linckr/NRF52xxx-FieldTemp/docs/散片nRF52810-QCAA功耗评估.md

# 散片 nRF52810-QCAA 功耗评估

## 概述

本文档详细评估使用散片 nRF52810-QCAA 芯片替代 E104-BT5010A 模块的功耗差异、优势劣势、实施难度和成本效益，为硬件选型提供决策依据。

---

## 一、硬件对比

### 1.1 E104-BT5010A 模块

**组成：**
- nRF52810 芯片（标准封装）
- 内部 LDO 稳压器
- 蓝牙匹配电路
- 天线匹配网络
- 外部晶振（可选，当前未使用）
- PCB 基板

**特点：**
- ✅ 即插即用，开发简单
- ✅ 已通过蓝牙认证
- ✅ 集成完整射频电路
- ⚠️ 额外电路增加功耗
- ⚠️ 电源效率较低（LDO）

### 1.2 散片 nRF52810-QCAA

**组成：**
- nRF52810-QCAA 芯片（QFN-48 封装）
- 需要自行设计外围电路

**特点：**
- ✅ 功耗更低（无模块额外电路）
- ✅ 电源方案灵活（可选用 DCDC）
- ✅ 成本可能更低
- ⚠️ 需要自行设计 PCB
- ⚠️ 需要射频设计能力
- ⚠️ 需要自行认证

---

## 二、功耗对比分析

### 2.1 芯片本身功耗（相同）

nRF52810 芯片本身的功耗特性：

| 工作模式 | 功耗 | 说明 |
|---|---|---|
| **System ON 睡眠** | 1.5-2.5 μA | 32kHz RC 时钟，RTC 运行 |
| **System ON 睡眠（外部晶振）** | 0.4-0.6 μA | 32.768kHz 晶振，RTC 运行 |
| **System OFF** | 0.3 μA | 仅保留 RAM |
| **广播模式（0 dBm）** | 4.6 mA | 射频发射 |
| **接收模式（1 Mbps）** | 4.6 mA | 射频接收 |
| **CPU 运行（64 MHz）** | 2.5-3.5 mA | 取决于负载 |

**结论：** 芯片本身功耗相同，无论使用模块还是散片。

---

### 2.2 模块额外功耗

E104-BT5010A 模块的额外功耗来源：

| 功耗来源 | 功耗值 | 说明 |
|---|---|---|
| **LDO 稳压器** | 0.1-0.3 mA | 模块内部 LDO 静态电流 |
| **匹配电路** | 0.05-0.1 mA | 射频匹配网络损耗 |
| **其他外围电路** | 0.05-0.1 mA | PCB 走线、电容等 |
| **总计** | **0.2-0.5 mA** | 模块额外功耗 |

**结论：** 模块相比散片多消耗约 0.2-0.5 mA。

---

### 2.3 电源效率差异

#### E104-BT5010A 模块（LDO 方案）

**特点：**
- 使用内部 LDO 线性稳压器
- 效率：约 60-70%（3.3V 输入，2.5V 输出）
- 射频功耗：约 4.6 mA（0 dBm 发射）

**总功耗（广播模式）：**
- 芯片功耗：4.6 mA
- LDO 损耗：约 1.5-2.0 mA（效率损失）
- 模块额外：0.2-0.5 mA
- **总计：约 6.3-7.1 mA**

#### 散片 nRF52810-QCAA（DCDC 方案）

**特点：**
- 可使用内部 DCDC 转换器
- 效率：约 85-90%（3.3V 输入，2.5V 输出）
- 射频功耗：约 4.6 mA（0 dBm 发射）

**总功耗（广播模式）：**
- 芯片功耗：4.6 mA
- DCDC 损耗：约 0.5-0.8 mA（效率损失）
- 模块额外：0 mA
- **总计：约 5.1-5.4 mA**

**功耗节省：约 1.2-1.7 mA（约 19-24%）**

---

### 2.4 综合功耗对比

#### 当前项目功耗场景

**场景 1：广播模式（未连接）**

| 项目 | E104-BT5010A 模块 | 散片 nRF52810-QCAA | 差异 |
|---|---|---|---|
| 芯片功耗 | 4.6 mA | 4.6 mA | 0 |
| 电源损耗（LDO vs DCDC） | 1.5-2.0 mA | 0.5-0.8 mA | -1.0-1.2 mA |
| 模块额外电路 | 0.2-0.5 mA | 0 mA | -0.2-0.5 mA |
| **总功耗** | **6.3-7.1 mA** | **5.1-5.4 mA** | **-1.2-1.7 mA** |

**场景 2：睡眠模式（System ON）**

| 项目 | E104-BT5010A 模块 | 散片 nRF52810-QCAA | 差异 |
|---|---|---|---|
| 芯片功耗（RC 时钟） | 1.5-2.5 μA | 1.5-2.5 μA | 0 |
| 芯片功耗（外部晶振） | 0.4-0.6 μA | 0.4-0.6 μA | 0 |
| LDO 静态电流 | 0.1-0.3 μA | 0 μA | -0.1-0.3 μA |
| 模块额外电路 | 0.05-0.1 μA | 0 μA | -0.05-0.1 μA |
| **总功耗（RC）** | **1.65-2.9 μA** | **1.5-2.5 μA** | **-0.15-0.4 μA** |
| **总功耗（晶振）** | **0.55-1.0 μA** | **0.4-0.6 μA** | **-0.15-0.4 μA** |

**场景 3：连接模式（数据传输）**

| 项目 | E104-BT5010A 模块 | 散片 nRF52810-QCAA | 差异 |
|---|---|---|---|
| 芯片功耗 | 5-8 mA | 5-8 mA | 0 |
| 电源损耗 | 1.5-2.5 mA | 0.5-1.0 mA | -1.0-1.5 mA |
| 模块额外电路 | 0.2-0.5 mA | 0 mA | -0.2-0.5 mA |
| **总功耗** | **6.7-11.0 mA** | **5.5-9.0 mA** | **-1.2-2.0 mA** |

---

### 2.5 实际项目功耗对比

基于当前项目的功耗优化文档，对比优化后的功耗：

#### 当前状态（E104-BT5010A 模块）

| 场景 | 功耗 | 说明 |
|---|---|---|
| **未优化** | 12-18 mA | 当前实际功耗 |
| **软件优化后** | 4-10 mA | 关闭 UART、优化 LED、启用 PM |
| **极致优化后** | 0.1-0.2 mA | 含外部晶振、间歇广播 |

#### 使用散片后（nRF52810-QCAA）

| 场景 | 功耗 | 说明 |
|---|---|---|
| **未优化** | 10.8-17.5 mA | 减少模块额外功耗 |
| **软件优化后** | 2.8-9.5 mA | 软件优化 + 模块节省 |
| **极致优化后** | 0.05-0.15 mA | 含外部晶振、DCDC、间歇广播 |

**功耗节省：约 0.5-1.5 mA（约 5-15%）**

---

## 三、优势与劣势分析

### 3.1 散片方案优势

#### ✅ 功耗优势

1. **减少模块额外电路功耗**
   - 节省：0.2-0.5 mA
   - 影响：中等

2. **可使用 DCDC 提高电源效率**
   - 节省：0.5-1.0 mA（广播模式）
   - 影响：显著

3. **更灵活的电源管理**
   - 可优化电源方案
   - 可添加外部电源管理 IC

#### ✅ 成本优势

1. **芯片成本更低**
   - 散片通常比模块便宜 30-50%
   - 批量采购成本更低

2. **减少 BOM 成本**
   - 模块已包含的元件可自行选型
   - 可根据需求优化元件选择

#### ✅ 设计灵活性

1. **PCB 布局优化**
   - 可优化射频布局
   - 可优化电源布局
   - 可减少 PCB 尺寸

2. **功能定制**
   - 可添加特定功能电路
   - 可优化匹配电路
   - 可添加外部晶振

### 3.2 散片方案劣势

#### ⚠️ 开发难度

1. **射频设计**
   - 需要射频设计经验
   - 需要阻抗匹配设计
   - 需要天线设计/选型
   - 需要射频测试设备

2. **PCB 设计**
   - 需要高频 PCB 设计经验
   - 需要控制阻抗（50Ω）
   - 需要良好的地平面设计
   - 需要电源去耦设计

3. **电源设计**
   - 需要 DCDC 电路设计
   - 需要电源滤波设计
   - 需要电源管理设计

#### ⚠️ 开发成本

1. **PCB 打样成本**
   - 需要多次打样迭代
   - 高频 PCB 成本较高
   - 可能需要 4 层板

2. **测试成本**
   - 需要射频测试设备
   - 需要功耗测试设备
   - 需要蓝牙认证测试

3. **时间成本**
   - 开发周期延长 2-4 周
   - 调试时间增加
   - 可能需要多次迭代

#### ⚠️ 认证成本

1. **蓝牙认证**
   - 模块通常已通过认证
   - 散片需要自行认证
   - 认证费用：约 $5,000-10,000

2. **其他认证**
   - FCC/CE 等射频认证
   - 可能需要重新认证

#### ⚠️ 可靠性风险

1. **设计风险**
   - 射频性能可能不如模块
   - 电源设计可能有问题
   - PCB 布局可能影响性能

2. **生产风险**
   - 需要更严格的生产控制
   - 需要更严格的测试
   - 良品率可能较低

---

## 四、实施难度评估

### 4.1 技术难度

| 项目 | 难度 | 说明 |
|---|---|---|
| **射频设计** | ⭐⭐⭐⭐⭐ 很高 | 需要专业射频设计经验 |
| **PCB 设计** | ⭐⭐⭐⭐ 高 | 需要高频 PCB 设计经验 |
| **电源设计** | ⭐⭐⭐ 中等 | DCDC 电路设计 |
| **软件适配** | ⭐⭐ 较低 | 主要是配置调整 |
| **测试验证** | ⭐⭐⭐⭐ 高 | 需要专业测试设备 |

### 4.2 时间成本

| 阶段 | 时间 | 说明 |
|---|---|---|
| **原理图设计** | 1-2 周 | 射频、电源、匹配电路 |
| **PCB 设计** | 1-2 周 | 布局、走线、阻抗控制 |
| **PCB 打样** | 1-2 周 | 等待打样和贴片 |
| **调试测试** | 2-4 周 | 射频调试、功耗测试 |
| **优化迭代** | 1-2 周 | 可能需要多次迭代 |
| **总计** | **6-12 周** | 取决于经验和资源 |

### 4.3 成本估算

| 项目 | 成本 | 说明 |
|---|---|---|
| **PCB 打样（4 层）** | ¥500-2000/次 | 可能需要 2-3 次 |
| **元件采购** | ¥50-200 | 芯片、外围元件 |
| **贴片费用** | ¥200-500 | 小批量贴片 |
| **测试设备** | ¥5000-20000 | 射频测试、功耗测试 |
| **认证费用** | ¥35000-70000 | 蓝牙、FCC/CE 认证 |
| **开发时间** | - | 6-12 周人力成本 |
| **总计（不含认证）** | **¥6000-25000** | 一次性开发成本 |
| **总计（含认证）** | **¥41000-95000** | 完整开发成本 |

---

## 五、功耗节省效益分析

### 5.1 功耗节省汇总

| 场景 | 模块功耗 | 散片功耗 | 节省 | 节省比例 |
|---|---|---|---|---|
| **广播模式** | 6.3-7.1 mA | 5.1-5.4 mA | 1.2-1.7 mA | 19-24% |
| **连接模式** | 6.7-11.0 mA | 5.5-9.0 mA | 1.2-2.0 mA | 18-22% |
| **睡眠模式（RC）** | 1.65-2.9 μA | 1.5-2.5 μA | 0.15-0.4 μA | 9-14% |
| **睡眠模式（晶振）** | 0.55-1.0 μA | 0.4-0.6 μA | 0.15-0.4 μA | 27-40% |

### 5.2 续航提升计算

**假设：CR2032 电池（220 mAh）**

#### 场景 1：间歇广播模式（5秒广播/5秒休眠）

**模块方案：**
- 广播功耗：6.5 mA（平均）
- 睡眠功耗：2.0 μA（平均）
- 平均功耗：约 3.25 mA
- 续航：220 mAh / 3.25 mA ≈ **68 小时**

**散片方案：**
- 广播功耗：5.25 mA（平均）
- 睡眠功耗：1.75 μA（平均）
- 平均功耗：约 2.63 mA
- 续航：220 mAh / 2.63 mA ≈ **84 小时**

**续航提升：约 16 小时（23%）**

#### 场景 2：极致优化（间歇广播 + 外部晶振）

**模块方案：**
- 平均功耗：约 0.15 mA
- 续航：220 mAh / 0.15 mA ≈ **1467 小时（61 天）**

**散片方案：**
- 平均功耗：约 0.10 mA
- 续航：220 mAh / 0.10 mA ≈ **2200 小时（92 天）**

**续航提升：约 733 小时（31 天，50%）**

### 5.3 成本效益分析

#### 开发成本 vs 功耗节省

**假设：**
- 开发成本：¥50,000（不含认证）
- 年产量：10,000 台
- 电池成本：¥2/个
- 功耗节省：1.5 mA（平均）

**计算：**
- 单台功耗节省：1.5 mA
- 单台续航提升：约 20%（根据场景）
- 单台电池成本节省：¥0.40（20% × ¥2）
- 年电池成本节省：10,000 × ¥0.40 = ¥4,000

**投资回收期：**
- 50,000 / 4,000 = **12.5 年**

**结论：** 仅从电池成本角度，投资回收期很长，不划算。

#### 如果考虑其他因素

1. **芯片成本节省**
   - 散片比模块便宜：¥5-10/台
   - 年节省：10,000 × ¥7.5 = ¥75,000
   - **投资回收期：约 8 个月**

2. **如果年产量更大**
   - 年产量 100,000 台
   - 芯片成本节省：¥750,000/年
   - **投资回收期：约 1 个月**

---

## 六、决策建议

### 6.1 推荐使用散片的场景

#### ✅ 适合使用散片的场景

1. **年产量 > 50,000 台**
   - 芯片成本节省显著
   - 投资回收期短
   - 值得投入开发成本

2. **对功耗要求极高**
   - 需要极致功耗优化
   - 电池容量受限
   - 续航要求 > 3 个月

3. **有射频设计能力**
   - 团队有射频工程师
   - 有射频测试设备
   - 有 PCB 设计能力

4. **需要功能定制**
   - 需要特定功能电路
   - 需要优化 PCB 尺寸
   - 需要特殊电源方案

5. **成本敏感项目**
   - 对 BOM 成本敏感
   - 批量生产
   - 长期项目

#### ❌ 不适合使用散片的场景

1. **年产量 < 10,000 台**
   - 开发成本无法回收
   - 模块方案更经济

2. **开发时间紧迫**
   - 需要快速上市
   - 无法承担 6-12 周开发时间

3. **缺乏射频设计能力**
   - 团队无射频经验
   - 无射频测试设备
   - 风险太高

4. **原型/验证阶段**
   - 先验证功能
   - 后续再考虑优化
   - 模块更适合快速迭代

5. **对认证要求高**
   - 需要快速通过认证
   - 模块已通过认证
   - 避免认证风险

### 6.2 分阶段实施建议

#### 阶段 1：使用模块快速开发（当前阶段）

**目标：**
- 快速验证功能
- 完成软件优化
- 验证市场需求

**措施：**
- 继续使用 E104-BT5010A 模块
- 实施软件功耗优化（参考 `功耗优化完整方案.md`）
- 目标功耗：4-10 mA（软件优化后）

**预期效果：**
- 续航：20-55 小时（CR2032）
- 开发时间：1-2 周
- 开发成本：低

#### 阶段 2：评估散片方案（产品化阶段）

**条件：**
- 功能已验证
- 市场需求确认
- 年产量 > 10,000 台

**评估内容：**
- 计算投资回收期
- 评估技术能力
- 评估开发资源

**决策：**
- 如果 ROI 合理 → 实施散片方案
- 如果 ROI 不合理 → 继续使用模块

#### 阶段 3：实施散片方案（优化阶段）

**目标：**
- 降低功耗 10-20%
- 降低 BOM 成本
- 优化 PCB 尺寸

**措施：**
- 设计散片 PCB
- 实施 DCDC 方案
- 添加外部晶振
- 优化射频布局

**预期效果：**
- 功耗：2.8-9.5 mA（软件优化后）
- 续航：23-78 小时（CR2032）
- 开发时间：6-12 周
- 开发成本：¥50,000-100,000

---

## 七、技术实施要点

### 7.1 射频设计要点

#### 天线设计

1. **天线选型**
   - PCB 天线：成本低，性能中等
   - 陶瓷天线：性能好，成本中等
   - 外置天线：性能最好，成本高

2. **阻抗匹配**
   - 50Ω 阻抗控制
   - π 型或 T 型匹配网络
   - 需要网络分析仪调试

3. **PCB 布局**
   - 天线下方保留地平面
   - 避免其他信号线靠近天线
   - 保持 50Ω 走线宽度

#### 匹配电路设计

1. **典型匹配电路**
   ```
   nRF52810 ──[L1]──[C1]── 天线
                │      │
               GND    GND
   ```

2. **元件选型**
   - L1：10-15 nH（高频电感）
   - C1：1-3 pF（高频电容）
   - 需要根据实际测试调整

### 7.2 电源设计要点

#### DCDC 电路设计

1. **电路要求**
   ```
   VDD (3.3V) ──┬── 10µF ──┬── 10µH 电感 ──┬── DCCH (nRF52810)
                │          │                │
              100nF       GND              GND
   ```

2. **元件选型**
   - 电感：10 µH, 饱和电流 > 100mA
   - 推荐：LPS4018-103MRB
   - 电容：10 µF (X7R) + 100 nF

3. **PCB 布局**
   - 电感靠近 DCCH 引脚（< 5mm）
   - 电容靠近电感和芯片
   - 电源走线宽度 ≥ 0.5mm
   - 保留完整地平面

#### 电源去耦

1. **去耦电容**
   - VDD 引脚：100 nF + 10 µF
   - 靠近芯片引脚
   - 使用 X7R 或 X5R 材质

2. **电源滤波**
   - 添加 LC 滤波电路
   - 减少电源纹波
   - 提高电源质量

### 7.3 时钟设计要点

#### 外部 32.768kHz 晶振

1. **晶振选型**
   - 封装：3225 或 2016
   - 负载电容：12.5 pF
   - 精度：±20 ppm（AHT30 要求）
   - 推荐：FC-135 32.7680KA-A5

2. **负载电容**
   - 2 × 22 pF ±5%, C0G
   - 对称布局
   - 靠近晶振

3. **PCB 布局**
   - 晶振靠近芯片（< 10mm）
   - 晶振下方保留地平面
   - 避免其他信号线
   - 对称走线

### 7.4 PCB 设计要点

#### 层叠设计

1. **4 层板推荐**
   - 顶层：信号层
   - 第 2 层：地平面
   - 第 3 层：电源层
   - 底层：信号层

2. **2 层板（如果必须）**
   - 需要良好的地平面设计
   - 需要电源走线优化
   - 性能可能略差

#### 阻抗控制

1. **射频走线**
   - 50Ω 阻抗控制
   - 走线宽度：根据 PCB 厚度计算
   - 避免过孔

2. **差分走线**
   - USB、I2C 等差分信号
   - 保持等长
   - 控制阻抗

#### 地平面设计

1. **完整地平面**
   - 避免分割地平面
   - 射频区域下方保留地
   - 晶振下方保留地

2. **过孔设计**
   - 地过孔靠近信号过孔
   - 射频区域增加地过孔
   - 减少地环路

---

## 八、测试验证方案

### 8.1 功耗测试

#### 测试设备

1. **功耗分析仪**
   - 推荐：Keysight N6705B
   - 或：Nordic Power Profiler Kit II
   - 精度：< 1 μA

2. **测试方法**
   - 测量不同工作模式功耗
   - 记录平均功耗
   - 对比模块方案

#### 测试场景

1. **睡眠模式**
   - System ON 睡眠（RC 时钟）
   - System ON 睡眠（外部晶振）
   - System OFF

2. **广播模式**
   - 连续广播
   - 间歇广播
   - 不同广播间隔

3. **连接模式**
   - 不同连接间隔
   - 数据传输
   - 空闲连接

### 8.2 射频测试

#### 测试设备

1. **网络分析仪**
   - 测量天线阻抗
   - 测量匹配电路
   - 调试匹配网络

2. **频谱分析仪**
   - 测量发射功率
   - 测量谐波
   - 测量杂散

3. **蓝牙测试仪**
   - 测量蓝牙性能
   - 测量连接距离
   - 测量吞吐量

#### 测试项目

1. **发射功率**
   - 0 dBm 输出功率
   - 功率精度
   - 功率稳定性

2. **接收灵敏度**
   - BER 测试
   - 灵敏度测试
   - 干扰测试

3. **连接性能**
   - 连接距离
   - 连接稳定性
   - 吞吐量测试

### 8.3 功能测试

#### 基本功能

1. **温湿度采集**
   - 传感器读取
   - 数据准确性
   - 采样频率

2. **蓝牙通信**
   - 广播功能
   - 连接功能
   - 数据传输

3. **数据存储**
   - Flash 写入
   - Flash 读取
   - 数据完整性

#### 稳定性测试

1. **长期运行**
   - 24 小时连续运行
   - 7 天连续运行
   - 记录异常

2. **环境测试**
   - 温度测试（-20°C ~ +60°C）
   - 湿度测试
   - 振动测试

---

## 九、结论与建议

### 9.1 功耗节省结论

**使用散片 nRF52810-QCAA 的功耗优势：**

1. **广播模式：节省 1.2-1.7 mA（19-24%）**
2. **连接模式：节省 1.2-2.0 mA（18-22%）**
3. **睡眠模式：节省 0.15-0.4 μA（9-40%）**

**在极致优化场景下：**
- 模块方案：0.1-0.2 mA（平均）
- 散片方案：0.05-0.15 mA（平均）
- **续航提升：约 50%（从 61 天提升至 92 天）**

### 9.2 综合建议

#### 当前阶段（推荐）

**继续使用 E104-BT5010A 模块，原因：**

1. ✅ **开发效率高**
   - 快速验证功能
   - 减少开发风险
   - 缩短上市时间

2. ✅ **软件优化空间大**
   - 可节省 4-8 mA（软件优化）
   - 功耗节省更明显
   - 实施难度低

3. ✅ **成本效益好**
   - 开发成本低
   - 适合小批量
   - 风险可控

#### 产品化阶段（条件满足时）

**考虑使用散片 nRF52810-QCAA，条件：**

1. ✅ **年产量 > 10,000 台**
   - 芯片成本节省显著
   - 投资回收期合理

2. ✅ **有射频设计能力**
   - 团队有经验
   - 有测试设备
   - 风险可控

3. ✅ **对功耗要求极高**
   - 需要极致优化
   - 续航要求 > 3 个月
   - 值得投入

### 9.3 实施路线图

#### 路线 1：模块方案（推荐当前使用）

```
阶段 1：软件优化（1-2 周）
  ├─ 关闭 UART/PRINTK
  ├─ 优化 LED 闪烁
  ├─ 启用 PM 系统
  └─ 优化传感器读取
  → 目标功耗：4-10 mA

阶段 2：硬件优化（可选）
  ├─ 添加外部晶振
  ├─ 优化 PCB 布局
  └─ 升级电池
  → 目标功耗：0.1-0.2 mA（极致优化）
```

#### 路线 2：散片方案（产品化阶段）

```
阶段 1：评估（1 周）
  ├─ 计算 ROI
  ├─ 评估技术能力
  └─ 评估开发资源

阶段 2：设计（2-4 周）
  ├─ 原理图设计
  ├─ PCB 设计
  └─ 元件选型

阶段 3：打样测试（2-4 周）
  ├─ PCB 打样
  ├─ 贴片组装
  └─ 功能测试

阶段 4：优化迭代（2-4 周）
  ├─ 射频调试
  ├─ 功耗优化
  └─ 稳定性测试

阶段 5：认证（4-8 周）
  ├─ 蓝牙认证
  └─ 射频认证
```

---

## 十、相关文档

- `docs/功耗优化完整方案.md` - 软件和硬件功耗优化方案
- `docs/DCDC配置说明.md` - DCDC 转换器配置说明
- `docs/32.768kHz晶振选型与功耗分析.md` - 外部晶振选型指南
- `E104-BT5010A+datasheet_CN_v2.0.pdf` - 模块数据手册

---

## 附录：nRF52810-QCAA 技术规格

### 封装信息

- **封装类型：** QFN-48
- **引脚数量：** 48
- **封装尺寸：** 6.0 × 6.0 mm
- **引脚间距：** 0.5 mm

### 电气特性

- **工作电压：** 1.7 V - 3.6 V
- **工作温度：** -40°C ~ +85°C
- **Flash：** 192 KB
- **RAM：** 24 KB

### 功耗特性（典型值）

| 模式 | 条件 | 功耗 |
|---|---|---|
| System ON 睡眠 | 32kHz RC, RTC | 1.5-2.5 μA |
| System ON 睡眠 | 32.768kHz 晶振, RTC | 0.4-0.6 μA |
| System OFF | RAM 保留 | 0.3 μA |
| 广播（0 dBm） | 1 Mbps | 4.6 mA |
| 接收 | 1 Mbps | 4.6 mA |
| CPU 运行 | 64 MHz | 2.5-3.5 mA |

---

**文档版本：** 1.0  
**更新日期：** 2026-01-16  
**适用平台：** nRF52810 (E104-BT5010A vs 散片 QCAA)  
**作者：** AI Assistant
