linckr/NRF52xxx-FieldTemp/docs/温湿度传感器选型对比.md

# 温湿度传感器选型对比：AHT30 vs SHT40

## 快速对比表

| 特性 | AHT30 | SHT40 | 推荐场景 |
|---|---|---|---|
| **温度精度** | ±0.3°C | ±0.2°C | SHT40 更精确 |
| **湿度精度** | ±2%RH | ±1.8%RH | SHT40 更精确 |
| **测量时间** | 80ms | 1.7~8.2ms | SHT40 快 10 倍 |
| **功耗** | 较高 | 超低 (0.4μA 待机) | SHT40 更省电 |
| **价格** | 低 (约 ¥3-5) | 较高 (约 ¥8-12) | AHT30 性价比高 |
| **CRC 校验** | 无 | 有 | SHT40 更可靠 |
| **加热器** | 无 | 有 | SHT40 适合高湿环境 |
| **I2C 地址** | 0x38 (固定) | 0x44/0x45 (可选) | SHT40 更灵活 |
| **供电电压** | 2.0~5.5V | 1.08~3.6V | AHT30 范围更广 |
| **封装尺寸** | 3.0×3.0mm | 1.5×1.5mm | SHT40 更小 |

## 详细对比

### 1. 精度对比

#### 温度精度

| 传感器 | 典型精度 | 最大误差 | 测量范围 |
|---|---|---|---|
| AHT30 | ±0.3°C | ±0.5°C | -40~85°C |
| SHT40 | ±0.2°C | ±0.4°C | -40~125°C |

结论：SHT40 精度更高，测量范围更广。

#### 湿度精度

| 传感器 | 典型精度 | 最大误差 | 测量范围 |
|---|---|---|---|
| AHT30 | ±2%RH | ±3%RH | 0~100%RH |
| SHT40 | ±1.8%RH | ±3.5%RH | 0~100%RH |

结论：SHT40 典型精度更高，但最大误差略大。

### 2. 性能对比

#### 测量速度

```
AHT30: 80ms (固定)
SHT40: 1.7ms (低精度) / 4.5ms (中精度) / 8.2ms (高精度)
```

SHT40 即使在高精度模式下，也比 AHT30 快近 10 倍。

#### 功耗对比

| 模式 | AHT30 | SHT40 |
|---|---|---|
| 待机 | ~1μA | 0.4μA |
| 测量 (1次/秒) | ~1.5μA | 0.8μA (高精度) |
| 测量 (1次/秒) | ~1.5μA | 0.3μA (低精度) |

结论：SHT40 功耗更低，尤其适合电池供电应用。

### 3. 功能对比

#### AHT30 特点

- 简单易用，无需复杂配置
- 固定测量模式，无需选择精度
- 价格便宜，性价比高
- 供电电压范围广 (2.0~5.5V)
- 无 CRC 校验，可靠性稍低

#### SHT40 特点

- 三种精度模式可选，灵活性高
- 内置加热器，可去除冷凝
- CRC-8 校验，数据更可靠
- 测量速度快，响应迅速
- 功耗超低，适合低功耗应用
- 可选 I2C 地址，支持多传感器
- 价格较高

### 4. 应用场景推荐

#### 选择 AHT30 的场景

1. **成本敏感项目**
   - 大批量生产
   - 预算有限
   - 对精度要求不高

2. **简单应用**
   - 室内温湿度监测
   - 家用温湿度计
   - 教育项目

3. **宽电压供电**
   - 需要 5V 供电
   - 电源电压不稳定

4. **快速原型开发**
   - 简单易用
   - 无需复杂配置

#### 选择 SHT40 的场景

1. **高精度要求**
   - 实验室环境监测
   - 医疗设备
   - 精密仪器

2. **低功耗应用**
   - 电池供电设备
   - 无线传感器节点
   - 可穿戴设备

3. **快速响应**
   - 需要快速采样
   - 实时监控
   - 动态环境监测

4. **高湿度环境**
   - 需要加热器去除冷凝
   - 浴室、厨房等高湿场所
   - 户外应用

5. **高可靠性要求**
   - 需要 CRC 校验
   - 关键应用
   - 长期稳定运行

6. **多传感器系统**
   - 同一 I2C 总线上需要多个温湿度传感器
   - 利用可选地址功能

### 5. 代码对比

#### AHT30 使用示例

```c
// 初始化
aht30_init(i2c_dev);

// 读取数据 (固定 80ms)
int32_t temp, humi;
aht30_read(&temp, &humi);

printk("温度: %d.%02d °C\n", temp / 100, abs(temp % 100));
printk("湿度: %d.%02d %%RH\n", humi / 100, humi % 100);
```

#### SHT40 使用示例

```c
// 初始化 (需要指定地址)
sht40_init(i2c_dev, SHT40_I2C_ADDR_A);

// 读取数据 (可选精度)
int32_t temp, humi;
sht40_read(&temp, &humi, SHT40_PRECISION_HIGH);  // 8.2ms

printk("温度: %d.%02d °C\n", temp / 100, abs(temp % 100));
printk("湿度: %d.%02d %%RH\n", humi / 100, humi % 100);

// 高湿度环境使用加热器
if (humi > 9000) {
    sht40_read_with_heater(&temp, &humi, SHT40_HEATER_200MW_0_1S);
}
```

### 6. 成本分析

#### 单片成本 (参考价格)

| 传感器 | 小批量 (1-10片) | 中批量 (100片) | 大批量 (1000片+) |
|---|---|---|---|
| AHT30 | ¥5-8 | ¥3-5 | ¥2-3 |
| SHT40 | ¥12-15 | ¥8-10 | ¥6-8 |

#### 总体拥有成本 (TCO)

考虑以下因素：

1. **开发成本**
   - AHT30: 简单，开发快
   - SHT40: 功能多，需要更多测试

2. **功耗成本**
   - 电池供电应用中，SHT40 可延长电池寿命
   - 长期运行，SHT40 更省电

3. **可靠性成本**
   - SHT40 有 CRC 校验，减少错误数据
   - 减少售后维护成本

4. **性能收益**
   - SHT40 测量快，可提高系统响应速度
   - 高精度可提升产品竞争力

### 7. 迁移建议

#### 从 AHT30 迁移到 SHT40

如果你的项目已经使用 AHT30，但需要更高性能，迁移很简单：

```c
// 原 AHT30 代码
aht30_init(i2c_dev);
aht30_read(&temp, &humi);

// 迁移到 SHT40 (最小改动)
sht40_init(i2c_dev, SHT40_I2C_ADDR_A);
sht40_read(&temp, &humi, SHT40_PRECISION_HIGH);
```

主要改动：
1. 初始化时指定 I2C 地址
2. 读取时选择精度模式
3. 可选：利用加热器功能
4. 可选：读取序列号

#### 硬件改动

- I2C 地址不同 (AHT30: 0x38, SHT40: 0x44)
- 封装尺寸不同 (需要修改 PCB)
- 引脚兼容 (VDD, GND, SCL, SDA)

### 8. 推荐决策树

```
开始
  |
  ├─ 预算有限？
  |    └─ 是 → 选择 AHT30
  |
  ├─ 需要高精度？
  |    └─ 是 → 选择 SHT40
  |
  ├─ 电池供电？
  |    └─ 是 → 选择 SHT40
  |
  ├─ 需要快速响应？
  |    └─ 是 → 选择 SHT40
  |
  ├─ 高湿度环境？
  |    └─ 是 → 选择 SHT40 (有加热器)
  |
  ├─ 需要多个传感器？
  |    └─ 是 → 选择 SHT40 (可选地址)
  |
  └─ 简单应用？
       └─ 是 → 选择 AHT30
```

## 总结

### AHT30 适合：
- 成本敏感项目
- 简单温湿度监测
- 快速原型开发
- 对精度要求不高的场景

### SHT40 适合：
- 高精度要求
- 低功耗应用
- 快速响应需求
- 高湿度环境
- 高可靠性要求
- 多传感器系统

### 最终建议

1. **新项目**: 优先考虑 SHT40，性能更好，功耗更低
2. **成本敏感**: 选择 AHT30，性价比高
3. **高端产品**: 选择 SHT40，提升产品竞争力
4. **大批量生产**: 根据成本和性能需求权衡

两款传感器都是优秀的选择，关键是根据你的具体需求和预算做出决策。
