linckr/NRF52xxx-FieldTemp/PROTOCOL.md

# PROTOCOL.md — Firmware ↔ Android 接口协议

> 本文**从固件与 Android 两端代码逐字段交叉核对**得出，不是设计稿。
> 核对来源：
> - 固件：`src/ble/ble_ota.h`、`src/ble/ble_ota.c`、`src/ble/ble_services.h`、`src/main.c`、
>   `src/common.h`、`src/storage/w25q64.h`
> - Android：`data/bluetooth/BleConstants.kt`、`data/device/parser/*.kt`、`data/ota/*.kt`
>
> 全部数值一律 **小端序（little-endian）**，除非特别注明。

---

## 0. 总览：服务与特征

| 服务 | 服务 UUID | 特征 | 特征 UUID | 属性 | CCC | 用途 |
|---|---|---|---|---|---|---|
| 配置 | `12340020-1234-5678-1234-56789abcdef0` | 历史记录间隔 | `12340021-…` | READ / WRITE | 无 | uint16 秒（60~3600） |
| | | 设备状态 | `12340022-…` | READ / NOTIFY | 有 | 12 B |
| | | 历史数据 | `12340023-…` | WRITE / NOTIFY | 有 | 写 4 B timestamp / 5 B 显式请求；通知最多60 B |
| | | 温度极值 | `12340024-…` | READ / NOTIFY | 有 | 12 B |
| | | 温度极值重置 | `12340025-…` | WRITE | 无 | 写任意值即重置 |
| | | 历史信息 | `12340026-…` | READ | 无 | 8 B |
| | | **时间同步** | `12340011-…` | WRITE | 无 | 4 B Unix 秒 |
| 实时数据 | `12340030-1234-5678-1234-56789abcdef0` | 实时数据 | `12340031-…` | READ / NOTIFY | 有 | **8 B**（6 B 基础 + 2 B 电压） |
| 清空数据 | `12340040-1234-5678-1234-56789abcdef0` | 清空数据 | `12340041-…` | WRITE | 无 | 未启用保留时写任意非空值异步清空；保留启用后拒绝 |
| **OTA** | `12340050-1234-5678-1234-56789abcdef0` | Control | `12340051-…` | WRITE | 无 | 控制命令 |
| | | Data | `12340052-…` | **WRITE WITHOUT RESPONSE** | 无 | 镜像分片 |
| | | Status | `12340053-…` | NOTIFY | 有 | 12 B 状态 |

UUID 全称规则：`1234 00XX 1234 5678 1234 56789abcdef0`，完整写法例如
`12340021-1234-5678-1234-56789abcdef0`。固件与 Android 各自声明这些 UUID；任何变更都必须
同时核对 `ble_services.h` / `ble_ota.h` 与 `BleConstants.kt`。

### 时间同步与电池电压的归属

- 固件没有 `12340010` 服务；时间同步特征 `12340011` 属于配置服务 `12340020`。
- `12340026` 只表示历史信息。Android 已删除早期与它冲突的 `BATTERY_CHAR` 别名。
- 电池电压通过实时数据帧的 offset 6 上报。

---

## 1. 广播与设备名

| 项目 | 值 |
|---|---|
| 广播名 | `PandaTemp_XXXX`，`XXXX` = `%02X%02X` 形式的蓝牙地址低两字节（**反序**：`val[1]` 在前） |
| 名称来源 | `src/ble/ble_adv.c:60`，`snprintf(..., "%s_%02X%02X", DEVICE_NAME_BASE, addrs[0].a.val[1], addrs[0].a.val[0])` |
| 实测例 | `PandaTemp_7086` |
| 连接数 | `CONFIG_BT_MAX_CONN=1` —— **同一时刻只允许 1 个连接** |
| 配对/绑定 | 关闭（`CONFIG_BT_SMP=n`、`CONFIG_BT_BONDABLE=n`、`CONFIG_BT_MAX_PAIRED=0`），**无加密** |
| 广播标志 | `BT_LE_AD_GENERAL | BT_LE_AD_NO_BREDR` |

Android 侧的名称过滤常量（`BleConstants`）：`PandaTemperatureEX` / `PandaTemperature` /
前缀 `Panda` / `yodfz-temp` / 前缀 `yodfz`。当前固件名 `PandaTemp_7086` 命中前缀 `Panda`。

---

## 2. 配置服务

### 2.1 历史记录间隔 `12340021`（READ / WRITE，uint16）

| 偏移 | 长度 | 类型 | 端序 | 说明 |
|---|---:|---|---|---|
| 0 | 2 | uint16 | LE | 历史记录落盘周期（秒） |

- 有效范围 **60 ~ 3600**（`MIN_HISTORY_INTERVAL = 60`，`MAX_HISTORY_INTERVAL = 3600`）。
  下限 60 是**容量红线**（65000 × 60 s = 45.1 天，产品承诺 30 天），不是性能取舍。
- 写入后固件会**立即通知**同特征上的新值（`interval_char_data`）。
- ⚠️ 语义变更：旧固件（v2 及更早）该特征表示"采集间隔"，采样与落盘共用同一周期。
  新固件（1.0.6+0 起）表示"历史记录落盘周期"，采样**固定 1 秒**。
  App 通过状态帧 `byte5` 的 `bit0 (CAP_HISTORY_INTERVAL)` 区分。

### 2.2 设备状态 `12340022`（READ / NOTIFY，**12 字节**）

| 偏移 | 长度 | 类型 | 端序 | 说明 |
|---|---:|---|---|---|
| 0 | 2 | uint16 | LE | 历史记录间隔（秒） |
| 2 | 2 | uint16 | LE | 已存储记录数（超过 65535 时截断为 0xFFFF） |
| 4 | 1 | uint8 | — | 状态位，见下表 |
| 5 | 1 | uint8 | — | 能力位，见下表（旧固件恒 0） |
| 6 | 2 | uint16 | LE | 固件版本号 —— **新固件为 patch 号**（1.0.8 → `8`；旧固件为主/次编码） |
| 8 | 2 | uint16 | LE | 采样间隔（恒为 `1`） |
| 10 | 2 | uint16 | LE | 名义天数：启用策略按limit，否则按65000；capacity×interval/86400取整，上限0xFFFF |

**byte4 状态位**

| Bit | 宏 | 含义 |
|---|---|---|
| 0 | — | 已连接（`bt_connected`） |
| 1 | — | 时间已同步（含仅从 NVS 恢复的旧时间） |
| 2 | — | 正在清空或执行历史保留维护；忙时暂停历史请求 |
| 3 | — | **墙钟可信**：本次上电收到过手机对时。仅从 NVS 恢复旧时间时为 0 |

**byte5 能力位**（`src/main.c:882-887`）

| Bit | 宏 | 含义 |
|---|---|---|
| 0 | `CAP_HISTORY_INTERVAL 0x01` | `12340021` 已改为"历史记录间隔"语义 |
| 1 | `CAP_SAMPLE_FIXED 0x02` | 采样固定 1 秒，不可配置 |
| 2 | `CAP_EVENT_RECORDS 0x04` | 支持突变/越限事件记录 |
| 3 | `CAP_AVERAGE_RECORDS 0x08` | 历史记录为周期均值 |
| 4 | `CAP_WALLCLOCK_ALIGN 0x10` | 周期记录时间戳按墙钟边界对齐（60→`:00`；300→`:00/:05/…） |
| 5 | `CAP_PARTIAL_WINDOW 0x20` | 对时后首个窗口可能短于一个周期（保留而非丢弃） |
| 6 | `CAP_HISTORY_VOLTAGE 0x40` | 支持显式请求14 B含电压历史；不能仅凭此位假定已协商 |
| 7 | `CAP_HISTORY_RETENTION 0x80` | 支持HISTORY特征的持续3000条保留命令 |

源码 v9 上报 `caps = 0xFF`；v8 历史基线为 `0x3F`。新固件已真机运行，cap255与V3 raw3000条回读通过；保留冷启动持久性已通过真实断电及raw集合验证；数据库迁移已完成，最新Live回归通过。

Android 解析：`DeviceStatusParser`（支持 5 / 7 / 8 / 10 / 12 字节，缺失字段取默认值）。

### 2.3 历史信息 `12340026`（READ，**8 字节**）

| 偏移 | 长度 | 类型 | 端序 | 说明 |
|---|---:|---|---|---|
| 0 | 4 | uint32 | LE | 总记录数 |
| 4 | 2 | uint16 | LE | 起始扇区（有数据时为最旧扇区号，否则 0） |
| 6 | 2 | uint16 | LE | 起始记录索引（保留窗口可能为非0；从此精确位置开始读） |

### 2.4 温度极值 `12340024`（READ / NOTIFY，**12 字节**）

| 偏移 | 长度 | 类型 | 端序 | 说明 |
|---|---:|---|---|---|
| 0 | 2 | int16 | LE | 最高温度（0.01 °C） |
| 2 | 4 | uint32 | LE | 最高温度发生时间（Unix 秒） |
| 6 | 2 | int16 | LE | 最低温度（0.01 °C） |
| 8 | 4 | uint32 | LE | 最低温度发生时间（Unix 秒） |

特殊值（`MaxMinTempParser`）：最高温和 `-32768(0x8000)` 且时间戳 0 → 未记录/已重置；
最低温和 `32767(0x7FFF)` 且时间戳 0 → 未记录/已重置。

> 当前固件发送 12 字节。Android 解析器仍兼容旧固件的 4 字节格式。

### 2.5 温度极值重置 `12340025`（WRITE）

写入**任意长度任意内容**即触发重置，并通知手机新值。无固定报文格式。

### 2.6 时间同步 `12340011`（WRITE，**4 字节**）

| 偏移 | 长度 | 类型 | 端序 | 说明 |
|---|---:|---|---|---|
| 0 | 4 | uint32 | LE | Unix 时间戳（秒） |

- 长度必须 **恰好 4**，否则返回 `BT_ATT_ERR_INVALID_ATTRIBUTE_LEN`。
- 小于 `946684800`（2000-01-01 UTC）时**只打印警告、仍然接受**。
- 效果：置 `time_base_timestamp` / `time_base_uptime`、`time_synced = true`、
  **`wall_clock_aligned = true`**（状态帧 bit3 置 1）、**重算历史结算网格**、立即写入 NVS。
- 只动聚合窗口与结算网格，**不碰 NVS 写头与已有历史**。

### 2.7 清空数据 `12340041`（WRITE）

未启用保留策略且无维护任务时，写入任意非空值即触发**异步**清空（`clear_data_work_handler`，逐扇区擦除 256 个扇区）。
立即返回，不阻塞 GATT 响应。清空期间状态帧 bit2 置 1。
无固定报文格式。

---

## 3. 历史数据（`12340023`）

### 3.1 BLE 记录格式：V2 12 B / V3 14 B

| 偏移 | 长度 | 类型 | 说明 |
|---|---:|---|---|
| 0 | 4 | uint32 LE | Unix秒 |
| 4 | 2 | int16 LE | 温度0.01°C |
| 6 | 2 | uint16 LE | 湿度0.01%RH |
| 8 | 4 | uint32 LE | 气压Pa，发送时从存储字还原；App除100得到hPa |
| 12 | 2 | uint16 LE | 仅V3：采集时缓存电压mV；0xFFFF为未知/无效 |

旧存量没有历史电压，V3回读时填0xFFFF；不得用当前VDD补写旧记录。
App仅凭明确能力位及请求选格式，绝不按patch号或包长度猜测。

### 3.2 显式历史请求与通知

所有请求写 HISTORY `12340023`；offset必须为0，长度仅4或5 B。

| 请求 | 能力前提 | 含义 |
|---|---|---|
| `[timestamp LE32]` 4 B | 原有历史功能 | V2 12 B；0拉全量，正数只取timestamp更大的记录 |
| `[timestamp LE32, 03]` 5 B | `0x40` | 明确选择V3 14 B；timestamp语义同上 |
| `[3000 LE32, 04]` 5 B | `0x80`且操作已授权 | 启用持续保留最近3000条，不是历史timestamp请求 |

当前固件的保留命令只接受3000；60秒周期的3000条仅约2.08天，事件记录还可能缩短时间范围。旧固件拒绝5 B长度；发送新命令前必须核对能力，
**绝不能失败后回退写CLEAR `12340041`**：旧固件的CLEAR会对任意非空写入全量擦除。
未知尾操作码返回VALUE_NOT_ALLOWED；维护中、活动传输或无效保留数量返回WRITE_NOT_PERMITTED。
新连接默认V2；4 B请求恢复V2，5 B尾03只影响当前会话。格式请求须先成功，再启用CCC。

通知缓存仍60 B：V2最多5×12=60 B，V3最多4×14=56 B，尾包按整条记录截断。
结束标志仍为独立1 B `FF`，另有原有4 B总数通知，不属于历史记录。

### 3.3 Flash 内部编码：保持12 B，无批量迁移

`struct data_record`、地址跨度和页几何保持12 B、21条/页、336条/扇区。
只有offset8的32-bit存储字有新编码，**磁盘内容不再直接等同BLE气压字段**：

| bits31:30 | 含义 |
|---|---|
| `00` | 旧格式：完整uint32气压Pa；历史电压未知 |
| `11` | 新记录暂存，未提交，不可回传 |
| `10` | 新记录已提交；bits17:0气压Pa，bits29:18电压mV，4095为未知 |
| `01` | 不支持的格式，跳过 |

气压合法范围10000–200000 Pa，可用18 bits无损表示；电压12 bits可表示0–4094 mV。
先写暂存12 B并读回比对，再对offset11清bit6形成已提交标记，最后读回确认才推进有效写入。
整个12 B全FF才为空槽；非空撕裂槽占用、跳过，不在原地址覆盖。
提交已成功但应答失败时，重试识别相同已提交记录，不重复追加。
BLE发送先解码气压；旧App继续读12 B，不需要了解内部编码。
旧固件降级会将新编码气压判断为异常，不能作为支持的历史降级路径。

### 3.4 持续保留3000条：原子窗口与安全回收

原始记录必须先完整留档；裁剪不是自动连接操作，也不是全量清空。
收到合法命令后置状态byte4 bit2维护忙，分步从写头反向选择最近3000条有效已提交记录，
不足3000则保留全部。最近按存储顺序计算，不根据错误/未来年份猜排序。
独立NVS key7保存magic/version、limit、写头、精确首记录、数量和回收起点；旧keys1–3保持兼容。
提交并读回验证成功后，才回收窗口外完整旧扇区；首扇区旧前缀仅1→0零化，绝不擦除其有效尾部。
中途掉电重启时根据原子检查点及实际已占用/有效槽恢复窗口，回收幂等继续。
每次新记录提交后窗口前移；跨扇区才写检查点，不逐条改NVS。
历史信息总数、起始sector/index及新旧格式回读都遵守该窗口。
策略启用后CLEAR请求被拒绝，避免全量清空使持久化窗口失配。

此设计保持secondary/NVS/history既有地址及容量；native C故障注入通过不等同真实拔电验证，
已完成开发信任链 1.0.9 升级与主槽逐字节回读、V3 历史回读和硬件精确保留3000条；P3已取得擦除流程、部分写入、END后和暂停搬运流程的真实电池断电恢复证据，但不证明 NOR/NVMC 忙脉冲中断电。保留策略冷启动持久性已验证；realme到小米数据库迁移已完成；持续App3000策略retain验收通过，最新Live回归已通过；生产信任链部署待完成。 具体证据与测试边界见HANDOFF最新阶段记录。

---

## 4. 实时数据 `12340031`（READ / NOTIFY）

| 偏移 | 长度 | 类型 | 端序 | 说明 |
|---|---:|---|---|---|
| 0 | 2 | int16 | LE | 温度（0.01 °C，有符号） |
| 2 | 2 | uint16 | LE | 湿度（0.01 %RH） |
| 4 | 2 | uint16 | LE | 气压（**0.1 hPa**，由 Pa/10 得到，下限 0、上限 0xFFFF） |
| 6 | 2 | uint16 | LE | **电池电压（mV）** —— 仅当 `CONFIG_ADC=y` 时存在 |

- 帧长：`REALTIME_FRAME_LEN` = **8**（有 ADC）/ **6**（无 ADC）。当前发布构建为 **8**。
- 传感器读取失败时对应字段填 **0**（不是哨兵值）。
- 电压无效哨兵 **`0xFFFF`**；App 必须显示 `--`，绝不能显示成 65.535 V。
- ⚠️ 注意偏移 4 的单位与 §3.1 不同：**实时帧是 0.1 hPa，历史记录是 Pa**。
  这是历史遗留的不一致，两侧代码都按此解析，**当前不改**（改就是破坏兼容性）。
- 主动上报：需要在 `12340031` 上订阅 NOTIFY；1 Hz 采样触发通知。
  也可在 `12340031` 上直接 READ（读时现场刷新）。

Android 解析：`RealtimeDataParserV2`（`data/device/parser/RealtimeDataParser.kt`）。
它先判 `0xFFFF` 哨兵，再用 **1700~3600 mV** 量程做第二道防线（nRF52810 工作电压范围），
任一命中即置 `null`。

---

## 5. OTA 协议

服务 `12340050`，三特性：Control `12340051`（WRITE）、Data `12340052`（WRITE WITHOUT RESPONSE）、
Status `12340053`（NOTIFY）。

### 5.1 Control 命令（写 `12340051`）

| 操作码 | 名称 | 长度 | 有效状态 |
|---|---|---:|---|
| `0x01` | START | **61** | 任意（会中止上一次会话） |
| `0x02` | END | 1 | `READY` / `RECEIVING` |
| `0x03` | CANCEL | 1 | 任意 |
| `0x04` | TRIGGER | 1 | **仅 `VERIFY`** |

**START 报文（61 字节）**

| 偏移 | 长度 | 类型 | 端序 | 说明 |
|---|---:|---|---|---|
| 0 | 1 | uint8 | — | `0x01` |
| 1 | **16** | bytes | — | OTA 授权密钥（与固件 `OTA_AUTH_KEY` 逐字节相同） |
| 17 | 4 | uint32 | LE | 镜像总字节数 `total` |
| 21 | **8** | bytes | — | 镜像头偏移 `0x14` 起的 8 字节 `ih_ver`（**原样透传，不解析**） |
| 29 | **32** | bytes | — | **整个 `zephyr.signed.bin`** 的 SHA-256 |

长度不等于 61 → `err=9 (LEN)`；密钥不符 → `err=1 (AUTH)`。

**START 是异步的**：回调只做校验 + 拷贝 + `k_work_submit()`，整槽擦除（约 1~2 s）在工作队列执行。
**在收到 `state=READY` 之前，Data 写入会被拒绝**（回调返回 `BT_ATT_ERR_UNLIKELY`）。
客户端**必须**等 `READY`，`IDLE 且 err=0` 不等于可以发数据。

### 5.2 Data（写 `12340052`）

- 内容：`zephyr.signed.bin` 的顺序分片，纯追加，**无序号、无 offset、无每包校验**。
- 分片大小 = 协商 MTU − 3（ATT 写头）。MTU 128 → 125 B；回退 MTU 65 → 62 B。
- 只允许在 `READY` / `RECEIVING` 状态写。
- 累计字节数超过 START 声明的 `total` → `err=5 (SIZE)`。
- 环形缓冲（2 × 256 B）被打满 → **`err=11 (OVERRUN)` 保护性中止**（不静默丢数据），
  客户端应从 START 重发（设备按已确认偏移续传）。

### 5.3 Status 通知（`12340053`，**12 字节**）

| 偏移 | 长度 | 类型 | 端序 | 说明 |
|---|---:|---|---|---|
| 0 | 4 | uint32 | LE | **已写入 Flash 的连续偏移**（confirmed offset） |
| 4 | 4 | uint32 | LE | 镜像总字节数 `total` |
| 8 | 1 | uint8 | — | `state` |
| 9 | 1 | uint8 | — | `err` |
| 10 | 1 | uint8 | — | 进度百分比（`confirmed × 100 / total`） |
| 11 | 1 | uint8 | — | flags，**预留，恒 0** |

⚠️ `offset` 是**已落 Flash** 的连续偏移，**刻意滞后**于已接收字节数
（数据先进 256 B 缓冲，凑满一页才落盘）。**流控必须以它为准**，不能用"我发了多少"。

**发送时机**：`START` 完成（READY）、状态每次变化、以及**每收满 8 个 Data 包**
（`OTA_ACK_PACKETS = 8`）各通知一次。不逐包确认是刻意的（逐包 notify 会抢 ACL 缓冲与射频时间）。

**state（`enum ota_state`）**

| 值 | 名称 | 含义 |
|---:|---|---|
| 0 | `IDLE` | 空闲（START 准备期也报这个） |
| 1 | `READY` | 已擦除/已定位，**可以发数据** |
| 2 | `RECEIVING` | 接收中 |
| 3 | `VERIFY` | 字节数 / magic / 版本 / SHA-256 全部通过，可 TRIGGER |
| 4 | `PENDING` | 已 `boot_request_upgrade()`，即将重启 |
| 5 | `ERROR` | 出错，看 `err` |

**err（`enum ota_err`）**

| 值 | 名称 | 含义 |
|---:|---|---|
| 0 | `NONE` | 无错误 |
| 1 | `AUTH` | 密钥不匹配 |
| 2 | `STATE` | 当前状态不允许该操作 |
| 3 | `TOO_LARGE` | 超过次级槽容量（**擦除前**拒绝） |
| 4 | `FLASH` | 擦/写失败 |
| 5 | `SIZE` | 接收字节数与声明不符 |
| 6 | `MAGIC` | 镜像 magic 不对 |
| 7 | `VERSION` | 镜像 `ih_ver` 与 START 声明不符 |
| 8 | `HASH` | App 侧 SHA-256 校验失败（`CONFIG_IMG_ENABLE_IMAGE_CHECK=y` 时启用） |
| 9 | `LEN` | Control 报文长度非法 |
| 10 | `INTERNAL` | 内部错误 |
| 11 | `OVERRUN` | 接收环形缓冲被打满，保护性中止（可从已确认偏移重发 START 续传） |

### 5.4 断点续传

- 续传状态存在 **NVS `NVS_ID_OTA`**：

| 字段 | 类型 | 说明 |
|---|---|---|
| `offset` | uint32 | 已写入的连续偏移 |
| `total` | uint32 | 声明的总字节数 |
| `ih_ver[8]` | bytes | 镜像版本 |
| `img_id[16]` | bytes | **SHA-256 的前 16 字节** |
| `valid` | uint8 | 1 = 有效 |

- **续传判定必须同时比对 `total` + `ih_ver` + `img_id`**。
  只用 `(total, ih_ver)` 会把两个"同版本同大小但内容不同"的镜像错误拼接。
- 命中续传时，`resume_off = offset & ~(IMG_BLOCK_BUF_SIZE - 1)`（**向下对齐到 256 B**），
  **跳过整槽擦除**，从该偏移继续。
- 任一项不符 → 清掉续传状态、整槽重来。
- `CANCEL` 与 `TRIGGER` 都会清除续传状态。

### 5.5 重连 / 超时 / 重启

| 行为 | 固件侧 | Android 侧（`OtaRunner` / `OtaConstants`） |
|---|---|---|
| 断线重连 | 设备侧续传状态保留在 NVS，重连后重新 START 即可 | 每次重试**重新扫描**，不沿用旧 `BLEDevice` |
| 等待 READY 超时 | — | `START_READY_TIMEOUT_MS = 15_000` |
| Status 超时 | — | `statusTimeoutMs = 8_000`（构造参数默认值） |
| 流控窗口 | 每 8 包通知一次已落盘偏移 | `FLOW_WINDOW_BYTES = 4 KiB`（未确认字节不超过该值） |
| OVERRUN 重试 | 置 `err=11` 并停止接收 | `MAX_OVERRUN_RESTARTS = 2`（从已确认偏移续传重发） |
| MTU | 请求 128，失败回退默认 | `PREFERRED_MTU=128`、`FALLBACK_MTU=65`、`MIN_START_MTU=64` |
| TRIGGER 后 | `sys_reboot(SYS_REBOOT_WARM)` | 写 TRIGGER 后设备复位会拉断链路，**应判为成功**。表象有两种：BLE 写返回 `status=133 (GATT_ERROR)`（Android 侧，见 `TRIGGER_DISCONNECT_GRACE_MS=100` × 15 步），或 WinRT 直接抛 `OSError [WinError -2147467260]`（PC 侧，已由 `tools/ota_host_client.py` 捕获） |

### 5.6 镜像类型（**必须传 `zephyr.signed.bin`**）

Android **必须**发送 `zephyr.signed.bin`，不能是：

| 文件 | 为什么不行 |
|---|---|
| `zephyr.bin` | 裸应用镜像，**没有 MCUboot 头与签名** → 设备 `err=6 MAGIC` |
| `merged.hex` | 是 hex 文本且包含 MCUboot，格式与分区语义都不同 |
| `zephyr.elf` | 调试用 ELF |
| `dfu_application.zip` | 是给 MCUboot **serial recovery** 用的容器；当前未启用该模式 |

原因：设备把收到的字节**原样写进次级槽**，然后由 MCUboot 按固定头
（magic `0x96F3B83D`、`ih_hdr_size=512`、`ih_img_size`@`0x0C`、`ih_ver`@`0x14`）
解析并做 **ECDSA-P256 验签**。只有 `zephyr.signed.bin` 同时具备头与签名。

Android 侧 `OtaImageParser` 在**发送前**就校验 magic 与大小，magic 不符会直接以
`OtaImageError.BadMagic` 拒绝，而不是等设备报错。

---

## 6. 版本与兼容性协商

### 6.1 有没有独立的 protocol version？

**没有独立的 protocol version 字段，也没有单独的协商握手特征。** App 读取状态能力位后，在 HISTORY 请求中明确选择格式：`0x40` 能力位与 5 B 请求尾字节 `03` 共同启用 V3；只有能力位或版本号都不能代替该请求。`0x80` 则允许显式保留命令。
双方使用以下状态字段与服务信息判断能力：

| 判断依据 | 位置 | 说明 |
|---|---|---|
| 状态帧长度 | `12340022` 的读出长度 | 5 / 7 / 8 / 10 / 12 字节，缺字段取默认值 |
| 状态帧 `byte5` 能力位 | 见 §2.2 | 旧固件恒 0 → App 走旧语义分支 |
| 状态帧 `byte6–7` 固件版本 | uint16 LE，patch 号 | 显示与日志；有效版本号可参与 V1/V2 合并实时固件识别，不能推断 V3 |
| 实时帧长度 | `12340031` | ≥ 8 字节才读取电压字段 |
| 是否有实时数据服务 `12340030` | 服务发现 | 无则按老 ESS 固件处理 |
| OTA 服务 `12340050` 是否存在 | 服务发现 | 无则无 OTA 能力 |

⚠️ **固件版本号不能用来推断协议**：新固件是 **patch 号**（`APP_PATCHLEVEL`），
老固件是主/次版本编码，两者共用同一个 `uint16` 位段。这是本项目最容易踩的坑
（历史记录 V3 错位事故的根因）。

### 6.2 Android 如何判断固件版本

1. 读 `12340022` → `DeviceStatusParser` 读取 `byte6–7` 的 uint16 LE → `firmwareVersion`（新固件为 patch 号）。
2. 用于**界面显示**（`v9` 之类）与**日志**；`DeviceProfileFactory` 也将有效版本号（>0）或实时数据服务存在作为合并实时固件的 V2/V1 识别依据。
3. **不通过版本号推断 V3 或历史记录长度**：`0x40` 能力位明确选择 V3 Profile，其请求追加 `03`；没有该位时沿用 V2/V1 路径。

### 6.3 Android 如何判断 OTA 能力

服务发现时看是否存在 `12340050`。当前没有"OTA 能力位"这种东西。
`FirmwareUpdateScreen` 在有 OTA 服务时可用。

### 6.4 镜像兼容性 / 最低固件要求

- 镜像与设备的兼容性**完全由 MCUboot 保证**：分区大小（≤ 160 KiB 次级槽）+ `ih_ver` +
  ECDSA-P256 签名（必须由同一把私钥签出）。
- **没有**"最低固件版本"检查，也**没有**防回滚（downgrade prevention）配置。
  推一个版本号更低的已签名镜像，MCUboot 会正常搬运。
- 次级槽容量上限 `0x28000` = 163,840 B；App 签名镜像红线 157,696 B。

---

## 7. 错误与边界行为速查

| 场景 | 固件行为 | App 应如何处理 |
|---|---|---|
| 写入长度非法的 Control 报文 | `err=9`；START 长度不对时不改状态 | 按 `err` 文案提示 |
| Data 在非 READY/RECEIVING 时写入 | 回调返回 `BT_ATT_ERR_UNLIKELY`，**不发通知** | 超时 → 提示"设备未就绪" |
| 设备状态长时间停在 `IDLE` | START 正在擦除（1~2 s） | 等 READY，最多 15 s |
| 收到 `err=11 OVERRUN` | 已停止接收，Flash 中数据完整 | 提示后从 START 重发（自动续传），最多 2 次 |
| 收到 `err=8 HASH` | 次要校验失败（MCUboot 才是最终防线） | 提示重传，**设备不会重启** |
| TRIGGER 后链路断开（`status=133` / WinRT `已中止操作`） | 设备正常复位 | **判为成功**，不要报错 |
| 广播里看不到设备 | `MAX_CONN=1`，可能已被别的手机占用 | 先断开其它连接 |

---

## 8. 已清理的遗留冲突

2026-09-15 已同步修正 README 的 LED 引脚、最高最低温度特征长度、MCU 型号、历史气压字段名，
并删除冲突的 Android `BATTERY_CHAR` 与未注册的固件 `12340010` 声明。历史设计文档仍可能描述
旧协议；当前协议只以本文件与两端代码为准。`OTA_AUTH_KEY` 继续由忽略文件注入，固件可信边界
仍是 MCUboot ECDSA-P256 验签。

### 2026-10-10 当前验收状态：App 1.1.2 / 持续3000条

当前App为versionCode4 / versionName1.1.2、Room11，手机安装Debug APK；Firmware为开发信任链1.0.9。124项JVM单元测试、10项isolated Room测试通过；生产1.1.2 APK v2/RSA3072验签通过、证书未变，尚未安装生产APK。最新Live连续全量/立即重试/中途断连/重连回归171.105 s通过；最终归档结果见本节末。

手机已完成realme完整数据库到小米迁移（主库SHA匹配源归档），原小米1,042条GPS已备份、未并入。随后按完整归档及硬件raw集合应用精简；早先一次精简后App增至3004而硬件仍3000，确认一次性精简不足，现已实现持续策略。最新明确retain真机36.388 s通过：硬件3000、App模块3000、手机来源样本208；启用标记已持久化。手机样本包含有/无GPS，模块3000不等于整个数据库总行数；隔离记录及私人完整档案仍保留本机，不上传。

持续策略按device显式启用：仅在retain3000命令得到count=3000且idle确认后保存本地prefs。对已启用且支持0x80的设备，每次历史同步发timestamp=0全量请求；只有本会话真实END、received=3000、唯一wire timestamps=3000、前后原始8 B HISTORY_INFO完全一致、所有upsert成功及连接/会话仍属于捕获目标时，才事务删除不在该实际wire集合的模块行。删除ID每批最多500，失败/取消/切换设备全部回滚、不删除；窗口不稳定最多自动重试一次。不能按时间排序取3000，缓存行可能比设备窗口更新。启用标记仅代表策略启用，不能代替每次精简成功证据。

Room11的isPhoneSample采用INTEGER NOT NULL DEFAULT0；新手机实时行始终true，即使没有GPS。10→11无损迁移把已有GPS行标为phone，旧无GPS来源未知保守默认false；在完整归档后按真实wire集合核对，不能靠年份猜测删除。历史DAO/count/增量仅处理false且geoNull；所有phone/GPS、隔离表和其他设备受保护。严格核心数值断言曾阻止单行旧手机实时/硬件差异的错误精简，没有通过放宽断言绕过。测试覆盖来源保护、精确164缓存差集、1201条跨删除批次、SQL中段abort和session失效原子回滚。

硬件3000策略已在隔离整根SWD后的实际电池断电冷启动验证：archive_sync23.296 s、完整3000及核心/GPS/无重复/未来检查通过；再次raw19.434 s通过（3000 V3、42000 B、END、8 B INFO稳定）。此前小米1.1.0 archive_sync79.289 s通过是历史证据；当前1.1.2也已独立完成Live回归，见本节末。VDD2.765 V为10/9约18:45观测、2.875 V为10/10约00:17 VM观测，均非当前实时读数，ADC仍未校准/无万用表对照。

P3四阶段已取得擦除流程、部分写入、END后及暂停MCUboot搬运的真实电池断电恢复证据；不证明NOR WIP/NVMC写脉冲被切断。SWD仍连接时曾出现W25Q64 init_res=22，根因未定，隔离SWD重试通过不等于已定位。旧v8硬件尾部14条曾被覆盖，timestamp/传感器数值14/14均在本机完整App档案保全；新恢复函数已有真实C回归与冷启动证据。

固件资源保持App Flash151540 B、RAM23080 B（余1496 B），MCUboot31876 B（余892 B），分区不变。DEV signed候选152203 B已真机回读；生产asset152202 B未部署，DER长度可变。两镜像App payload151540 B逐字节一致，SHA256 `236323e4319f7228ce6b4856bb1736a4bede1cf58e3dfc85239678bdc943494c`；完整signed文件不能混同。生产imgtool验证通过，但生产MCUboot公钥信任尚未部署、候选产物入口为 [v1.0.9-rc.1](https://github.com/linckr/NRF52xxx-FieldTemp/releases/tag/v1.0.9-rc.1)，发布状态以页面为准；两个upstream PR #2在最近记录时OPEN，后续实时核对。

持续策略与Live验收已完成，最终归档模块3000；生产信任部署与ADC校准仍是独立待办。

### 最终Live与一致归档验收

最终真机Live回归171.105 s通过：两次连续全量各3000、立即重试、收到部分记录后断连且全部既有模块ID未删除、重连及再次同步完成3000；仍保留窗口内记录ID/核心字段和所有既有手机样本，无重复/未来时间。重连首轮观察到0条历史、随后一次自动全量重试成功；本轮已由有界重试覆盖，但首次重连延迟为Medium性能边界，根因未定位。

最终只读一致归档（2026-10-10约01:12）SQLite integrity ok：模块3000、GPS187、无GPS手机样本31（受保护手机样本共218）、active3218、quarantine22484，未来时间0、模块重复0。Live期间VM电压开始2.886 V、结束2.868 V（本轮观测，不是ADC校准证明）。App已恢复运行；手机临时USB亮屏设置已恢复原值。私人数据库、档案路径、标识与归档内容不进Git。
