linckr/NRF52xxx-FieldTemp/docs/2026-02-10-Flash存储校验修复计划-plan.md

# Flash存储校验修复计划

## 需求背景

用户反馈设备显示存储了 12 条记录，但无法获取数据（读取失败或无数据返回）。
经分析，原因是启动时 `storage_init` 函数中的 NVS 位置校验逻辑存在缺陷：仅校验了写头位置是否为 `0xFF`（空），未校验写头之前的记录是否有效。
如果 Flash 被意外擦除（全 `0xFF`），但 NVS 中仍保留了之前的写入位置（如 `next_record_in_sector = 12`），校验会错误地通过，导致系统认为有数据，但在读取时遇到 `0xFF` 而失败。

## 实现方案

修改 `src/main.c` 中的 `storage_init` 函数，增强 NVS 位置校验逻辑：

1. 在校验写头位置为 `0xFF` 的同时，如果 `next_record_in_sector > 0`，额外校验前一条记录（`next_record_in_sector - 1`）是否有效（非 `0xFF`）。
2. 如果前一条记录也是 `0xFF`，说明 NVS 记录的位置无效（数据已丢失），应视为校验失败。
3. 校验失败后，系统会自动进入“重新定位”逻辑（二分法查找实际数据末尾），从而正确重置存储位置（归零或找到真实数据末尾）。

## 开发计划

- [x] 修改 `src/main.c` 中的 `storage_init` 函数，添加前一条记录的校验逻辑。
- [x] 验证编译通过。
