linckr/NRF52xxx-FieldTemp/docs/手机端温度计实现方案对比.md

# 手机端温度计实现方案对比（2026 年）

## 1. 需求分析

### 1.1 核心需求

- ✅ 支持 iOS 和 Android 双平台
- ✅ 无网环境下正常运行
- ✅ 通过蓝牙连接 E104-BT5010A 温湿度采集设备
- ✅ 实时显示温湿度数据
- ✅ 历史数据查看和管理

### 1.2 技术约束

- 设备：E104-BT5010A (nRF52810, BLE 5.0)
- 通讯协议：BLE GATT
- 运行环境：可能无网络连接
- 目标平台：iOS 13+ / Android 8.0+

---

## 2. 技术方案对比

### 方案一：原生 App 开发

#### 2.1 iOS 原生开发 (Swift/SwiftUI)

**技术栈：**

- Swift 5.9+ / SwiftUI
- Core Bluetooth 框架
- Xcode 15+

**优势：**

- ✅ **性能最优**：直接调用系统 API，无中间层损耗
- ✅ **功能完整**：完整访问 iOS 蓝牙 API，支持所有 BLE 特性
- ✅ **用户体验好**：原生 UI，流畅度高
- ✅ **离线运行**：完全本地运行，无需网络
- ✅ **系统集成**：可集成 iOS 通知、后台运行等特性
- ✅ **安全性高**：App Store 审核严格，用户信任度高
- ✅ **长期维护**：Apple 长期支持，API 稳定

**劣势：**

- ❌ **开发成本高**：需要分别开发 iOS 和 Android 版本
- ❌ **开发周期长**：两个平台需要两套代码
- ❌ **维护成本高**：需要维护两套代码库
- ❌ **技能要求高**：需要掌握 Swift 和 Java/Kotlin
- ❌ **发布流程复杂**：需要分别提交 App Store 和 Google Play

**适用场景：**

- 对性能要求极高
- 需要深度系统集成
- 有充足的开发资源
- 长期维护的产品

**开发示例：**

```swift
import CoreBluetooth

class BLEManager: NSObject, CBCentralManagerDelegate, CBPeripheralDelegate {
    var centralManager: CBCentralManager!
    var peripheral: CBPeripheral?

    func startScan() {
        centralManager.scanForPeripherals(withServices: nil, options: nil)
    }

    func centralManager(_ central: CBCentralManager,
                      didDiscover peripheral: CBPeripheral,
                      advertisementData: [String : Any],
                      rssi RSSI: NSNumber) {
        if peripheral.name == "PandaTemperature" {
            self.peripheral = peripheral
            centralManager.connect(peripheral, options: nil)
        }
    }
}
```

---

#### 2.2 Android 原生开发 (Kotlin/Java)

**技术栈：**

- Kotlin 1.9+ / Java 17+
- Android Bluetooth Low Energy API
- Android Studio / Jetpack Compose

**优势：**

- ✅ **性能最优**：直接调用 Android BLE API
- ✅ **功能完整**：完整访问 Android 蓝牙功能
- ✅ **用户体验好**：Material Design 原生体验
- ✅ **离线运行**：完全本地运行
- ✅ **系统集成**：可集成 Android 通知、后台服务等
- ✅ **灵活性高**：可自定义所有功能

**劣势：**

- ❌ **开发成本高**：需要分别开发 iOS 和 Android
- ❌ **Android 碎片化**：需要适配不同厂商和版本
- ❌ **BLE 兼容性**：不同厂商 BLE 实现有差异
- ❌ **发布流程**：需要 Google Play 审核

**适用场景：**

- 对性能要求高
- 需要深度定制
- 有 Android 开发经验
- 预算充足

**开发示例：**

```kotlin
class BLEManager(context: Context) {
    private val bluetoothAdapter: BluetoothAdapter? =
        (context.getSystemService(Context.BLUETOOTH_SERVICE) as BluetoothManager)
            .adapter

    fun startScan() {
        val scanner = bluetoothAdapter?.bluetoothLeScanner
        val filter = ScanFilter.Builder()
            .setDeviceName("PandaTemperature")
            .build()
        scanner?.startScan(listOf(filter), scanSettings, scanCallback)
    }
}
```

---

### 方案二：跨平台框架

#### 2.3 React Native

**技术栈：**

- React Native 0.72+
- react-native-ble-plx 或 react-native-ble-manager
- JavaScript/TypeScript

**优势：**

- ✅ **代码复用**：一套代码同时支持 iOS 和 Android
- ✅ **开发效率高**：使用熟悉的 Web 技术栈
- ✅ **热更新**：支持 OTA 更新（需要网络）
- ✅ **生态丰富**：大量第三方库
- ✅ **社区活跃**：Facebook 维护，社区支持好
- ✅ **离线运行**：打包后完全离线运行

**劣势：**

- ❌ **性能略低**：JavaScript 桥接有性能损耗
- ❌ **包体积大**：包含 JavaScript 引擎，体积较大
- ❌ **调试复杂**：需要同时调试原生和 JS 层
- ❌ **BLE 兼容性**：依赖第三方库，可能有兼容性问题
- ❌ **版本更新**：需要跟进 React Native 版本更新

**适用场景：**

- 有 Web 开发经验
- 需要快速开发
- 对性能要求不是极致
- 团队熟悉 JavaScript

**开发示例：**

```javascript
import { BleManager } from "react-native-ble-plx";

const manager = new BleManager();

manager.startDeviceScan(null, null, (error, device) => {
  if (error) {
    console.error(error);
    return;
  }
  if (device.name === "PandaTemperature") {
    manager.stopDeviceScan();
    device
      .connect()
      .then((device) => device.discoverAllServicesAndCharacteristics())
      .then((device) => {
        // 读取温湿度数据
      });
  }
});
```

---

#### 2.4 Flutter

**技术栈：**

- Flutter 3.16+
- flutter_blue_plus 或 flutter_reactive_ble
- Dart 语言

**优势：**

- ✅ **性能优秀**：编译为原生代码，性能接近原生
- ✅ **代码复用**：一套代码支持 iOS 和 Android
- ✅ **UI 一致**：跨平台 UI 表现一致
- ✅ **热重载**：开发体验好，快速迭代
- ✅ **Google 支持**：Google 官方维护
- ✅ **离线运行**：编译后完全离线
- ✅ **BLE 支持好**：有成熟的 BLE 插件

**劣势：**

- ❌ **学习曲线**：需要学习 Dart 语言
- ❌ **包体积大**：包含 Flutter 引擎，体积较大（20-30MB）
- ❌ **原生功能**：需要原生代码时，需要编写 Platform Channel
- ❌ **生态相对小**：相比 React Native 生态稍小

**适用场景：**

- 追求性能和开发效率平衡
- 愿意学习 Dart 语言
- 需要 UI 高度一致
- 团队有移动开发经验

**开发示例：**

```dart
import 'package:flutter_blue_plus/flutter_blue_plus.dart';

FlutterBluePlus.startScan(timeout: Duration(seconds: 4));

FlutterBluePlus.scanResults.listen((results) {
  for (ScanResult result in results) {
    if (result.device.name == 'PandaTemperature') {
      result.device.connect();
    }
  }
});
```

---

#### 2.5 Xamarin / .NET MAUI

**技术栈：**

- .NET MAUI 8.0+
- Plugin.BLE 或 Shiny.Ble
- C# 语言

**优势：**

- ✅ **代码复用**：一套 C# 代码支持多平台
- ✅ **性能好**：编译为原生代码
- ✅ **企业级**：Microsoft 支持，适合企业应用
- ✅ **类型安全**：C# 强类型，减少错误
- ✅ **离线运行**：编译后完全离线

**劣势：**

- ❌ **生态较小**：社区和库相对较少
- ❌ **学习成本**：需要 C# 和 .NET 知识
- ❌ **包体积**：包含 .NET 运行时
- ❌ **更新频率**：相比 React Native/Flutter 更新较慢

**适用场景：**

- 企业级应用
- 团队熟悉 .NET 技术栈
- 需要与 .NET 后端集成

---

### 方案三：Web 技术方案

#### 2.6 Web Bluetooth API (PWA)

**技术栈：**

- HTML5 / JavaScript
- Web Bluetooth API
- Service Worker (PWA)

**优势：**

- ✅ **开发简单**：使用 Web 技术，开发快速
- ✅ **无需安装**：浏览器直接访问
- ✅ **跨平台**：支持所有有浏览器的设备
- ✅ **更新方便**：服务器更新即可
- ✅ **成本低**：无需应用商店审核

**劣势：**

- ❌ **iOS 支持差**：iOS Safari 不支持 Web Bluetooth API（截至 2026 年）
- ❌ **需要 HTTPS**：生产环境必须 HTTPS（本地开发可用 localhost）
- ❌ **功能受限**：相比原生 API 功能有限
- ❌ **用户体验**：不如原生 App 流畅
- ❌ **离线能力**：需要 Service Worker，但功能有限

**适用场景：**

- 仅支持 Android 和桌面浏览器
- 快速原型开发
- 内部工具
- 不需要 iOS 支持

**开发示例：**

```javascript
navigator.bluetooth
  .requestDevice({
    filters: [{ name: "PandaTemperature" }],
    optionalServices: ["12340020-1234-5678-1234-56789abcdef0"],
  })
  .then((device) => device.gatt.connect())
  .then((server) =>
    server.getPrimaryService("12340020-1234-5678-1234-56789abcdef0")
  )
  .then((service) =>
    service.getCharacteristic("12340023-1234-5678-1234-56789abcdef0")
  )
  .then((characteristic) => {
    characteristic.addEventListener("characteristicvaluechanged", handleData);
    return characteristic.startNotifications();
  });
```

---

#### 2.7 微信小程序

**技术栈：**

- 微信小程序框架
- 微信 BLE API

**优势：**

- ✅ **无需安装**：微信内直接使用
- ✅ **开发简单**：使用 JavaScript，学习成本低
- ✅ **用户基数大**：微信用户覆盖广
- ✅ **审核快速**：相比应用商店审核更快
- ✅ **跨平台**：一套代码支持 iOS 和 Android
- ✅ **离线运行**：小程序可离线运行（已下载后）

**劣势：**

- ❌ **依赖微信**：必须在微信环境运行
- ❌ **功能受限**：受微信 API 限制
- ❌ **审核限制**：需要微信审核
- ❌ **数据隐私**：数据经过微信服务器
- ❌ **无法上架应用商店**：只能通过微信分发

**适用场景：**

- 目标用户主要在微信生态
- 快速上线
- 不需要独立 App
- 已有微信小程序开发经验

**备注：** 项目已有微信小程序接入方案文档，可参考 `docs/微信小程序接入方案.md`

---

#### 2.8 Capacitor / Cordova (混合 App)

**技术栈：**

- Capacitor 5+ 或 Cordova
- HTML/CSS/JavaScript
- 原生插件封装

**优势：**

- ✅ **Web 技术**：使用熟悉的 Web 技术栈
- ✅ **跨平台**：一套代码支持多平台
- ✅ **原生插件**：可调用原生功能
- ✅ **离线运行**：打包后完全离线
- ✅ **更新灵活**：支持热更新（需要网络）

**劣势：**

- ❌ **性能一般**：WebView 渲染，性能不如原生
- ❌ **用户体验**：UI 流畅度不如原生
- ❌ **调试复杂**：需要同时调试 Web 和原生层
- ❌ **插件依赖**：依赖第三方 BLE 插件质量

**适用场景：**

- 已有 Web 应用
- 需要快速迁移到移动端
- 对性能要求不高
- 团队主要是 Web 开发者

---

## 3. 方案对比总结表

| 方案 | 开发成本 | 性能 | iOS 支持 | Android 支持 | 离线运行 | 维护成本 | 推荐度 |
| --- | --- | --- | --- | --- | --- | --- | --- |
| iOS 原生 | 高 | ⭐⭐⭐⭐⭐ | ✅ | ❌ | ✅ | 高 | ⭐⭐⭐ |
| Android 原生  | 高 | ⭐⭐⭐⭐⭐ | ❌ | ✅ | ✅ | 高 | ⭐⭐⭐ |
| React Native  | 中 | ⭐⭐⭐⭐ | ✅ | ✅ | ✅ | 中 | ⭐⭐⭐⭐ |
| Flutter | 中 | ⭐⭐⭐⭐⭐ | ✅ | ✅ | ✅ | 中 | ⭐⭐⭐⭐⭐ |
| .NET MAUI | 中 | ⭐⭐⭐⭐ | ✅ | ✅ | ✅ | 中 | ⭐⭐⭐ |
| Web Bluetooth | 低 | ⭐⭐⭐ | ❌ | ✅ | ⚠️ | 低 | ⭐⭐ |
| 微信小程序 | 低 | ⭐⭐⭐ | ✅ | ✅ | ✅ | 低 | ⭐⭐⭐⭐ |
| Capacitor | 中 | ⭐⭐⭐ | ✅ | ✅ | ✅ | 中 | ⭐⭐⭐ |

---

## 4. 推荐方案

### 4.1 最佳推荐：Flutter

**推荐理由：**

1. ✅ **性能优秀**：编译为原生代码，性能接近原生 App
2. ✅ **开发效率高**：一套代码支持 iOS 和 Android
3. ✅ **BLE 支持完善**：有成熟的 `flutter_blue_plus` 插件
4. ✅ **离线运行**：完全支持无网环境
5. ✅ **UI 一致**：跨平台 UI 表现一致
6. ✅ **长期维护**：Google 官方支持，生态活跃

**实施建议：**

- 使用 `flutter_blue_plus` 插件处理 BLE 通讯
- 使用 `shared_preferences` 或 `sqflite` 存储历史数据
- 使用 `provider` 或 `riverpod` 进行状态管理
- 支持 iOS 13+ 和 Android 8.0+

---

### 4.2 次优推荐：React Native

**推荐理由：**

1. ✅ **开发快速**：使用 JavaScript，学习曲线平缓
2. ✅ **生态丰富**：大量第三方库和组件
3. ✅ **社区活跃**：问题容易找到解决方案
4. ✅ **代码复用**：一套代码支持双平台

**实施建议：**

- 使用 `react-native-ble-plx` 处理 BLE 通讯
- 使用 `@react-native-async-storage/async-storage` 存储数据
- 使用 Redux 或 Zustand 进行状态管理

---

### 4.3 快速方案：微信小程序

**推荐理由：**

1. ✅ **开发最快**：项目已有小程序接入方案
2. ✅ **无需安装**：用户直接使用
3. ✅ **用户覆盖广**：微信用户基数大
4. ✅ **审核快速**：相比应用商店更快

**适用场景：**

- 需要快速上线
- 目标用户主要在微信生态
- 不需要独立 App 品牌

---

### 4.4 高性能方案：原生开发

**推荐理由：**

1. ✅ **性能最优**：直接调用系统 API
2. ✅ **功能完整**：无任何限制
3. ✅ **用户体验最佳**：原生 UI 和交互

**适用场景：**

- 对性能要求极高
- 需要深度系统集成
- 有充足的开发资源
- 长期维护的产品

---

## 5. iOS 应用分发问题（重要）

### 5.1 核心问题

**重要提示：** Flutter 和 React Native 开发的 iOS 应用，**无法在没有 Apple 开发者账号的情况下直接分发给用户安装**。

iOS 系统有严格的安全机制：

- ✅ **Android**：可以直接生成 APK 文件，用户直接安装（无需账号）
- ❌ **iOS**：必须通过 Apple 的签名和分发机制，需要开发者账号

### 5.2 iOS 应用分发方式

#### 方式一：App Store 分发（需要付费开发者账号）

**要求：**

- Apple Developer Program 会员（$99/年）
- 通过 App Store 审核
- 用户从 App Store 下载安装

**优点：**

- ✅ 用户安装方便（从 App Store 搜索下载）
- ✅ 自动更新机制
- ✅ 用户信任度高
- ✅ 无设备数量限制

**缺点：**

- ❌ 需要付费（$99/年）
- ❌ 需要审核（通常 1-3 天）
- ❌ 审核规则严格

---

#### 方式二：TestFlight 内测分发（需要付费开发者账号）

**要求：**

- Apple Developer Program 会员（$99/年）
- 通过 TestFlight 审核（通常比 App Store 宽松）
- 用户需要安装 TestFlight App

**优点：**

- ✅ 可以分发给最多 10,000 名测试用户
- ✅ 审核相对宽松
- ✅ 可以收集反馈和崩溃报告

**缺点：**

- ❌ 需要付费（$99/年）
- ❌ 用户需要安装 TestFlight
- ❌ 测试版本有效期 90 天

---

#### 方式三：企业内部分发（需要企业开发者账号）

**要求：**

- Apple Enterprise Program（$299/年）
- 仅限企业内部员工使用
- 不能对外分发

**优点：**

- ✅ 无设备数量限制
- ✅ 无需 App Store 审核

**缺点：**

- ❌ 费用更高（$299/年）
- ❌ 仅限企业内部使用
- ❌ 申请条件严格（需要 D-U-N-S 编号）

---

#### 方式四：免费开发者账号（个人测试，限制多）

**要求：**

- 免费 Apple ID（无需付费）
- 仅限开发者自己使用
- 需要 Xcode 和 Mac 电脑

**限制：**

- ❌ **只能安装到自己的设备**（最多 3 台设备）
- ❌ **应用有效期 7 天**（7 天后需要重新签名安装）
- ❌ **无法分发给其他用户**
- ❌ 无法使用推送通知等高级功能

**适用场景：**

- 仅用于个人开发测试
- 学习 iOS 开发
- 不适合产品分发

---

#### 方式五：越狱设备安装（不推荐）

**要求：**

- 用户设备需要越狱
- 使用第三方工具安装（如 Cydia Impactor）

**缺点：**

- ❌ 用户设备需要越狱（风险高，不推荐）
- ❌ 违反 Apple 服务条款
- ❌ 安全性问题
- ❌ 普通用户不会越狱

**结论：不推荐此方式**

---

### 5.3 无开发者账号的替代方案

#### 方案 A：仅支持 Android（推荐）

**策略：**

- 使用 Flutter 或 React Native 开发
- **仅发布 Android 版本**
- iOS 用户使用其他方案（如微信小程序）

**优点：**

- ✅ Android 可以直接分发 APK，无需账号
- ✅ 开发成本低
- ✅ 用户安装方便

**缺点：**

- ❌ 无法覆盖 iOS 用户
- ❌ 需要为 iOS 用户提供替代方案

**实施：**

```bash
# Flutter 生成 Android APK
flutter build apk --release

# 生成的 APK 文件可以直接分发给用户安装
# 路径：build/app/outputs/flutter-apk/app-release.apk
```

---

#### 方案 B：使用微信小程序（最佳替代）

**策略：**

- iOS 和 Android 都通过微信小程序提供
- 无需开发者账号
- 无需应用商店审核

**优点：**

- ✅ **完全免费**（无需开发者账号）
- ✅ **支持 iOS 和 Android**
- ✅ **无需安装**（微信内直接使用）
- ✅ **审核快速**（通常 1-2 天）
- ✅ **项目已有接入方案**

**缺点：**

- ❌ 依赖微信环境
- ❌ 功能受微信 API 限制

**结论：这是无开发者账号情况下的最佳方案**

---

#### 方案 C：Web App（PWA）

**策略：**

- 开发 Web 应用（使用 Web Bluetooth API）
- 用户通过浏览器访问
- 可以添加到主屏幕（类似 App）

**优点：**

- ✅ 完全免费
- ✅ 无需开发者账号
- ✅ 无需应用商店
- ✅ 跨平台（但 iOS Safari 不支持 Web Bluetooth）

**缺点：**

- ❌ **iOS Safari 不支持 Web Bluetooth API**（关键限制）
- ❌ 仅适用于 Android 和桌面浏览器
- ❌ 用户体验不如原生 App

---

#### 方案 D：申请免费开发者账号（仅个人测试）

**适用场景：**

- 仅用于自己测试
- 学习开发
- 演示给少量用户（需要他们的设备 UDID）

**限制：**

- 最多 3 台设备
- 应用 7 天后过期
- 无法真正分发给用户

**申请步骤：**

1. 使用 Apple ID 登录 [developer.apple.com](https://developer.apple.com)
2. 同意开发者协议（免费）
3. 在 Xcode 中配置签名
4. 只能安装到自己的设备

---

### 5.4 方案对比总结

| 方案 | 需要开发者账号 | iOS 支持  | Android 支持 | 成本 | 推荐度 |
| --- | --- | --- | --- | --- | --- |
| **微信小程序** | ❌ 不需要 | ✅ | ✅ | 免费 | ⭐⭐⭐⭐⭐ |
| **仅 Android APK**  | ❌ 不需要 | ❌ | ✅ | 免费 | ⭐⭐⭐⭐ |
| **Web App (PWA)** | ❌ 不需要 | ❌ | ✅ | 免费 | ⭐⭐ |
| **App Store 分发**  | ✅ $99/年 | ✅ | ✅ | $99/年 | ⭐⭐⭐⭐ |
| **TestFlight 内测** | ✅ $99/年 | ✅ | ✅ | $99/年 | ⭐⭐⭐ |
| **免费开发者账号**  | ✅ 免费 | ⚠️ 仅自己 | ⚠️ 仅自己 | 免费 | ⭐ |

---

### 5.5 最终建议（无开发者账号）

#### 最佳方案：微信小程序

**理由：**

1. ✅ **完全免费**，无需开发者账号
2. ✅ **支持 iOS 和 Android**
3. ✅ **项目已有接入方案**（参考 `docs/微信小程序接入方案.md`）
4. ✅ **用户无需安装**，使用方便
5. ✅ **审核快速**（1-2 天）

**实施步骤：**

1. 参考项目现有文档开发小程序
2. 提交微信审核
3. 审核通过后用户即可使用

---

#### 备选方案：仅 Android + 微信小程序

**策略：**

- Android 用户：提供 APK 直接安装
- iOS 用户：使用微信小程序

**优点：**

- ✅ Android 用户获得完整原生体验
- ✅ iOS 用户通过小程序使用
- ✅ 完全免费

**缺点：**

- ❌ iOS 用户无法使用原生 App

---

#### 如果未来需要 iOS 原生 App

**建议：**

1. 先使用微信小程序验证产品
2. 产品成熟后，再考虑申请 Apple 开发者账号
3. 使用 Flutter/RN 开发，一套代码同时支持 iOS 和 Android
4. 提交 App Store 审核

**成本：**

- Apple Developer Program: $99/年
- 开发时间：如果已有 Flutter/RN 代码，iOS 版本几乎无需额外开发

---

### 5.6 常见问题 FAQ

**Q: Flutter/RN 开发的 iOS 应用，能否像 Android 一样直接安装？**
A: **不能**。iOS 系统要求所有应用必须经过 Apple 签名，这需要开发者账号。Android 可以直接安装 APK，但 iOS 不行。

**Q: 能否使用免费开发者账号分发给用户？**
A: **不能**。免费账号只能安装到自己的设备（最多 3 台），且应用 7 天后过期。无法真正分发给其他用户。

**Q: 能否通过其他方式绕过 Apple 的限制？**
A: 理论上可以通过越狱，但：

- 违反 Apple 服务条款
- 用户需要越狱设备（风险高）
- 普通用户不会这样做
- **不推荐此方式**

**Q: 微信小程序是否需要 Apple 开发者账号？**
A: **不需要**。小程序通过微信平台分发，无需 Apple 开发者账号。这是无账号情况下的最佳选择。

**Q: 如果只支持 Android，iOS 用户怎么办？**
A: 可以：

1. 为 iOS 用户提供微信小程序版本
2. 或者告知用户需要等待 iOS 版本（需要开发者账号）

**Q: 开发者账号费用是多少？**
A:

- 个人/公司账号：$99/年（美元），约 ¥700/年
- 企业账号：$299/年（美元），约 ¥2100/年

**Q: 能否先开发，后申请账号？**
A: **可以**。建议：

1. 先用微信小程序验证产品
2. 产品成熟后再申请开发者账号
3. 使用 Flutter/RN 可以快速生成 iOS 版本

---

## 6. 技术实现要点

### 5.1 BLE 连接管理

**关键点：**

- 设备扫描和过滤
- 连接状态管理
- 自动重连机制
- 连接超时处理

**实现建议：**

```dart
// Flutter 示例
class BLEConnectionManager {
  StreamSubscription<BluetoothConnectionState>? _connectionSubscription;

  Future<void> connect(BluetoothDevice device) async {
    await device.connect(
      timeout: Duration(seconds: 15),
      autoConnect: false,
    );

    _connectionSubscription = device.connectionState.listen((state) {
      if (state == BluetoothConnectionState.disconnected) {
        _handleDisconnection(device);
      }
    });
  }

  void _handleDisconnection(BluetoothDevice device) {
    // 实现自动重连逻辑
    Future.delayed(Duration(seconds: 2), () {
      device.connect();
    });
  }
}
```

---

### 5.2 数据存储（离线环境）

**方案选择：**

- **轻量数据**：使用 SharedPreferences / UserDefaults
- **结构化数据**：使用 SQLite (sqflite / react-native-sqlite-storage)
- **历史记录**：本地数据库存储

**实现建议：**

```dart
// Flutter SQLite 示例
class HistoryDatabase {
  static final HistoryDatabase instance = HistoryDatabase._init();
  static Database? _database;

  Future<Database> get database async {
    if (_database != null) return _database!;
    _database = await _initDB('history.db');
    return _database!;
  }

  Future<void> insertRecord(TemperatureRecord record) async {
    final db = await database;
    await db.insert('records', record.toMap());
  }

  Future<List<TemperatureRecord>> getAllRecords() async {
    final db = await database;
    final maps = await db.query('records', orderBy: 'timestamp DESC');
    return maps.map((map) => TemperatureRecord.fromMap(map)).toList();
  }
}
```

---

### 5.3 无网环境处理

**关键点：**

- 检测网络状态（但不依赖网络）
- 所有数据本地存储
- 离线功能完整可用
- 网络恢复后可同步（可选）

**实现建议：**

```dart
// 网络检测（仅用于提示，不影响功能）
class NetworkMonitor {
  static Future<bool> isOnline() async {
    try {
      final result = await InternetAddress.lookup('google.com');
      return result.isNotEmpty && result[0].rawAddress.isNotEmpty;
    } catch (_) {
      return false;
    }
  }

  // 但应用功能不依赖网络状态
  // 所有核心功能在离线状态下正常工作
}
```

---

### 5.4 数据同步（可选）

**如果未来需要云端同步：**

- 使用本地数据库作为主数据源
- 网络可用时后台同步
- 冲突解决策略（时间戳优先）

---

## 6. 开发时间估算

| 方案 | 开发时间 | 测试时间 | 总计 |
| --- | --- | --- | --- |
| Flutter | 3-4 周 | 1-2 周 | 4-6 周  |
| React Native | 3-4 周 | 1-2 周 | 4-6 周  |
| 微信小程序 | 1-2 周 | 1 周 | 2-3 周  |
| 原生开发 (双平台) | 6-8 周 | 2-3 周 | 8-11 周 |
| Web Bluetooth | 2-3 周 | 1 周 | 3-4 周  |

_注：时间估算基于有经验的开发团队_

---

## 7. 成本对比

| 方案 | 开发成本 | 维护成本 | 发布成本 | 总成本 |
| --- | --- | --- | --- | --- |
| Flutter | 中 | 中 | 低 | ⭐⭐ |
| React Native  | 中 | 中 | 低 | ⭐⭐ |
| 微信小程序 | 低 | 低 | 无 | ⭐ |
| 原生开发 | 高 | 高 | 中 | ⭐⭐⭐ |
| Web Bluetooth | 低 | 低 | 无 | ⭐ |

---

## 8. 最终建议

### 8.1 如果追求最佳平衡：**Flutter**

- 性能优秀，开发效率高
- 一套代码支持双平台
- BLE 支持完善
- 适合长期维护

### 8.2 如果追求快速上线：**微信小程序**

- 开发最快
- 已有接入方案
- 用户覆盖广
- 适合 MVP 验证

### 8.3 如果追求极致性能：**原生开发**

- 性能最优
- 功能完整
- 用户体验最佳
- 适合高端产品

### 8.4 如果团队是 Web 背景：**React Native**

- 学习曲线平缓
- 生态丰富
- 开发效率高
- 适合 Web 团队转型

---

## 9. 参考资料

- [Flutter BLE 插件文档](https://pub.dev/packages/flutter_blue_plus)
- [React Native BLE 插件文档](https://github.com/dotintent/react-native-ble-plx)
- [Web Bluetooth API 规范](https://web.dev/bluetooth/)
- [微信小程序 BLE API](https://developers.weixin.qq.com/miniprogram/dev/api/device/bluetooth/wx.openBluetoothAdapter.html)
- 项目现有文档：
  - `docs/安卓端开发通讯技术方案.md`
  - `docs/微信小程序接入方案.md`
  - `docs/温湿度蓝牙传输方案.md`

---

**文档版本**: v1.0  
**更新日期**: 2026-01-16  
**作者**: AI Assistant
