linckr/NRF52xxx-FieldTemp/20260116-104604.jpg

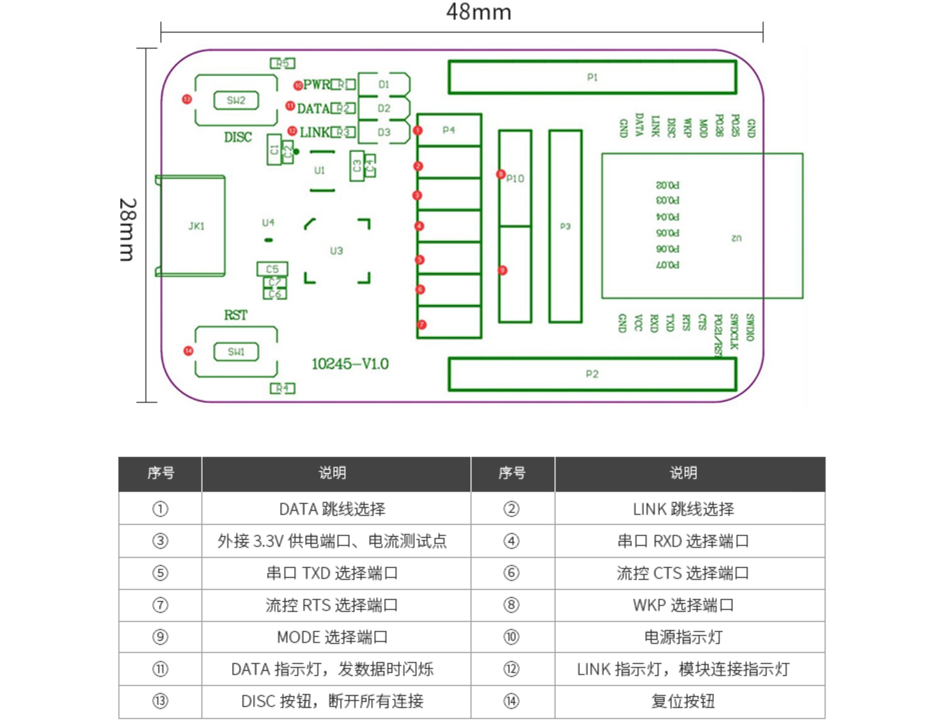
20260116-104604.jpg
