linckr/NRF52xxx-FieldTemp/20260116-104614.jpg

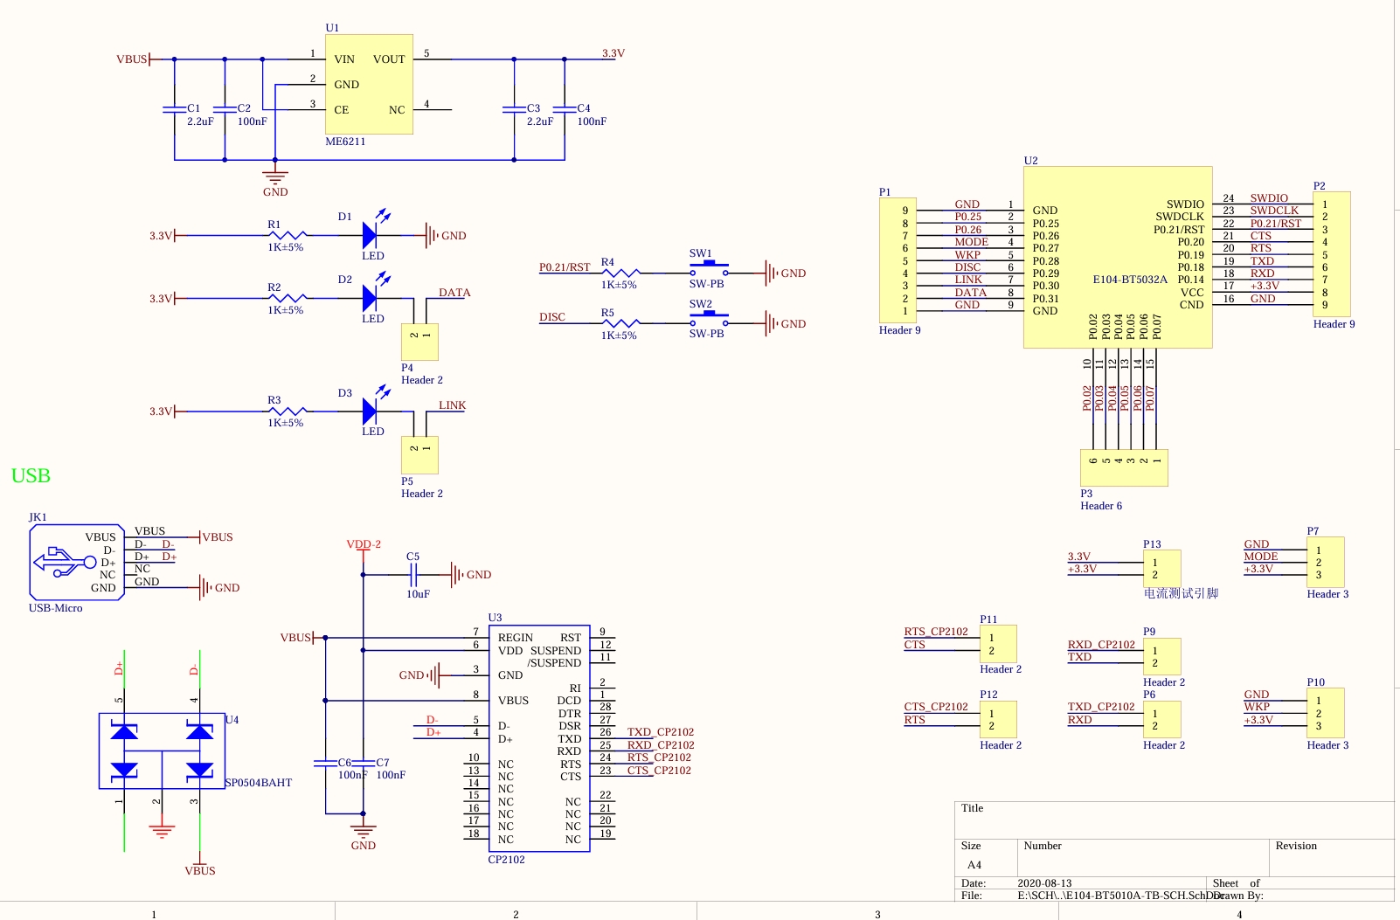
20260116-104614.jpg
